zenmanenergy/TeslaTurbine/Pulsejet/200mm/DXF/detonation chamber/spark-plug-61.snapshot.13/Renderings/Spark Plug - side view.png

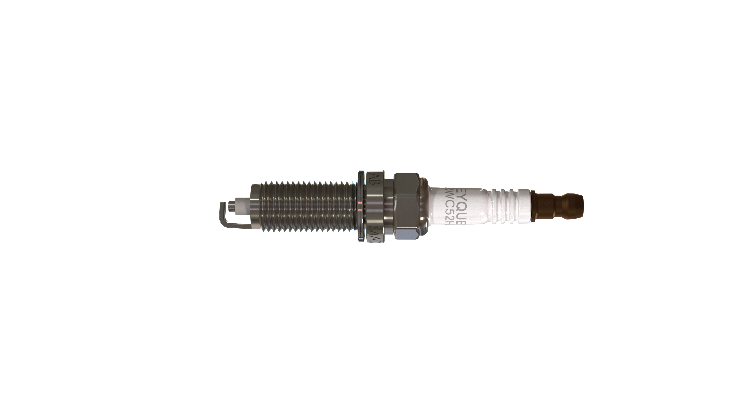
Pulsejet/200mm/DXF/detonation chamber/spark-plug-61.snapshot.13/Renderings/Spark Plug - side view.png
