zenmanenergy/TeslaTurbine/Pulsejet/200mm/DXF/valvular conduit/Tesla-Valve-US1329559-0.png

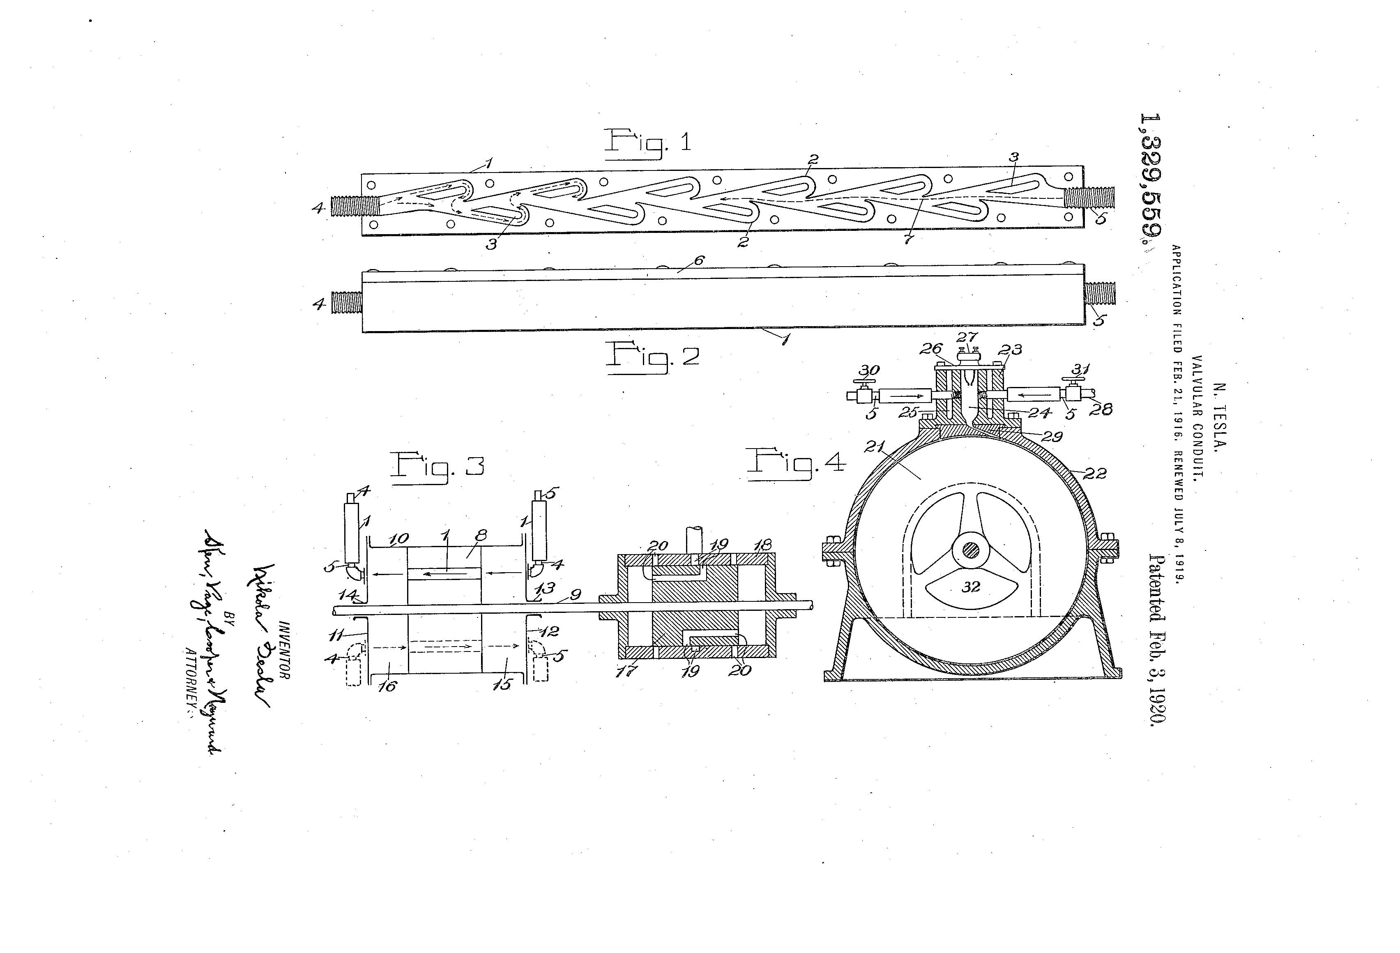
Pulsejet/200mm/DXF/valvular conduit/Tesla-Valve-US1329559-0.png
