zenmanenergy/TeslaTurbine/Pump/138mm/Solidworks 2015/renderings/Tesla Pump.JPG

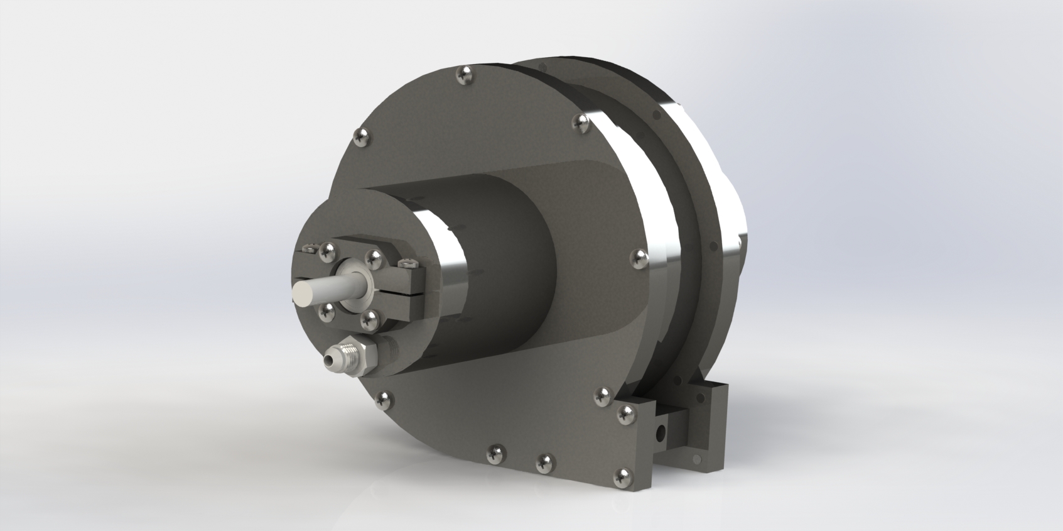
Pump/138mm/Solidworks 2015/renderings/Tesla Pump.JPG
