zenmanenergy/TeslaTurbine/Pulsejet/200mm/DXF/detonation chamber/combustion chamber.SLDASM

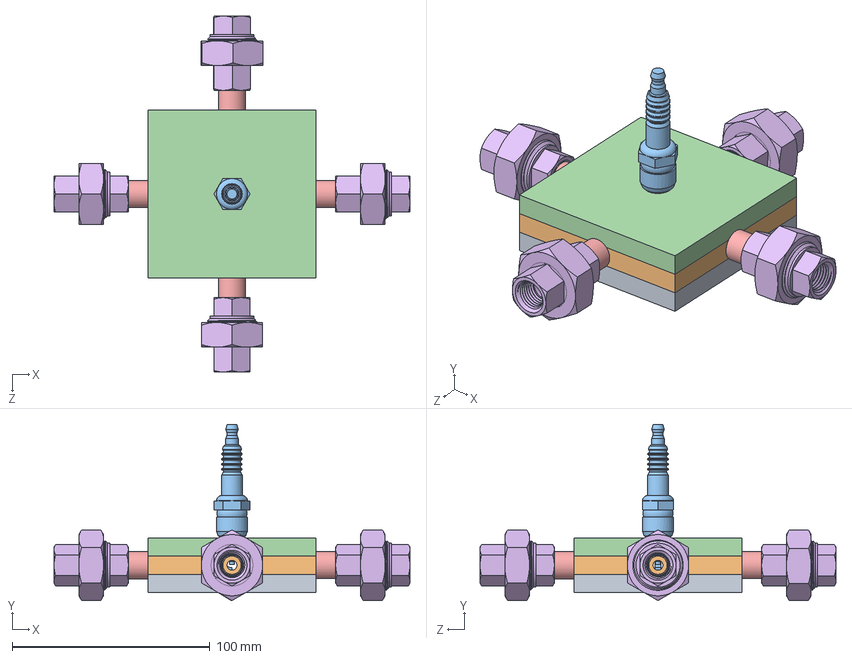
[picture p24: CAD file, 2020-06-17]
Pulsejet/200mm/DXF/detonation chamber/combustion chamber.SLDASM
180.1 x 89.1 x 180.1 mm
combustion chamber
chamber walls
SW3dPS
combustion top
9157K110_STD-WALL 304-304L SS THRD ONE END PIPE NIPPLE x 4
4464K484_TYPE 304 STAINLESS STL THREADED PIPE FITTING x 4
