zenmanenergy/TeslaTurbine/Pump/138mm/Solidworks 2015/magnetic bearings/magnetic bearings.SLDASM

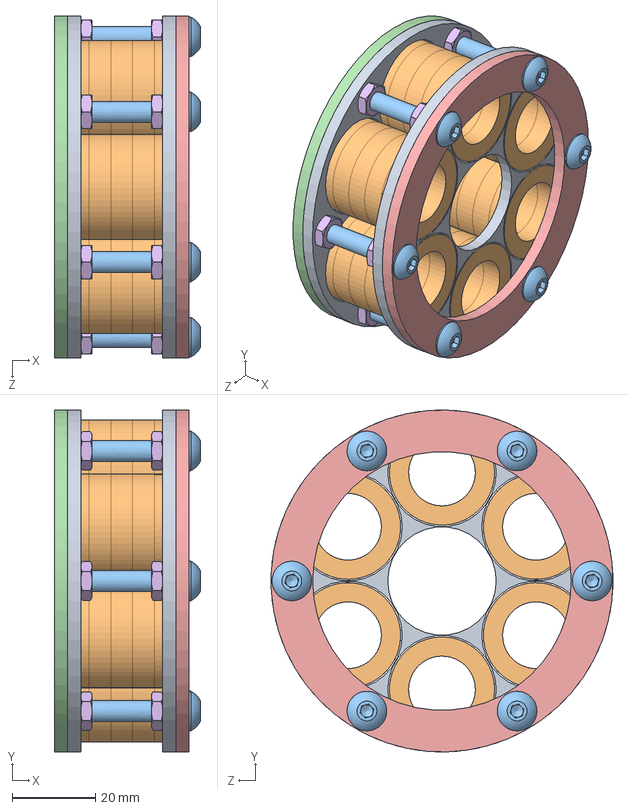
[picture p25: CAD file, 2020-10-07]
Pump/138mm/Solidworks 2015/magnetic bearings/magnetic bearings.SLDASM
35.1 x 82.0 x 82.0 mm
magnet plate x 2
25x16x5 neodymium bearing x 30
socket button head cap screw_am x 6
magnet holder nut
magnet holder
hex nut jam_am x 12
