zenmanenergy/TeslaTurbine/Pulsejet/200mm/DXF/detonation chamber/combustion chamber with propane.SLDASM

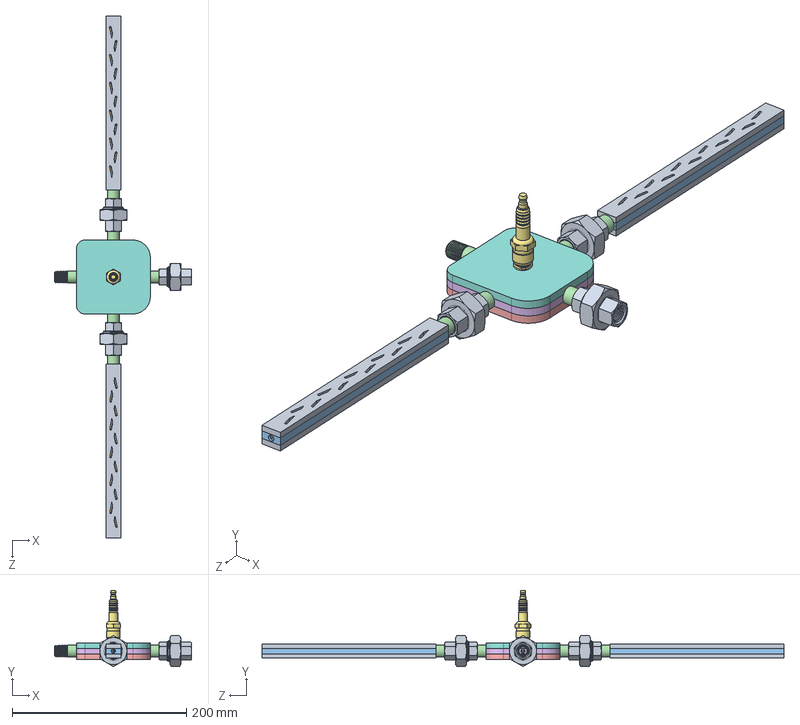
[picture p26: CAD file, 2020-06-17]
Pulsejet/200mm/DXF/detonation chamber/combustion chamber with propane.SLDASM
157.9 x 87.6 x 600.0 mm
bottom x 4
diverter x 22
channel x 2
9157K110_STD-WALL 304-304L SS THRD ONE END PIPE NIPPLE x 6
combustion chamber
chamber walls
SW3dPS
combustion top
4464K484_TYPE 304 STAINLESS STL THREADED PIPE FITTING x 3
