zenmanenergy/TeslaTurbine/Pump/138mm/Solidworks 2015/magnetic bearings/magnetic bearing stack.SLDASM

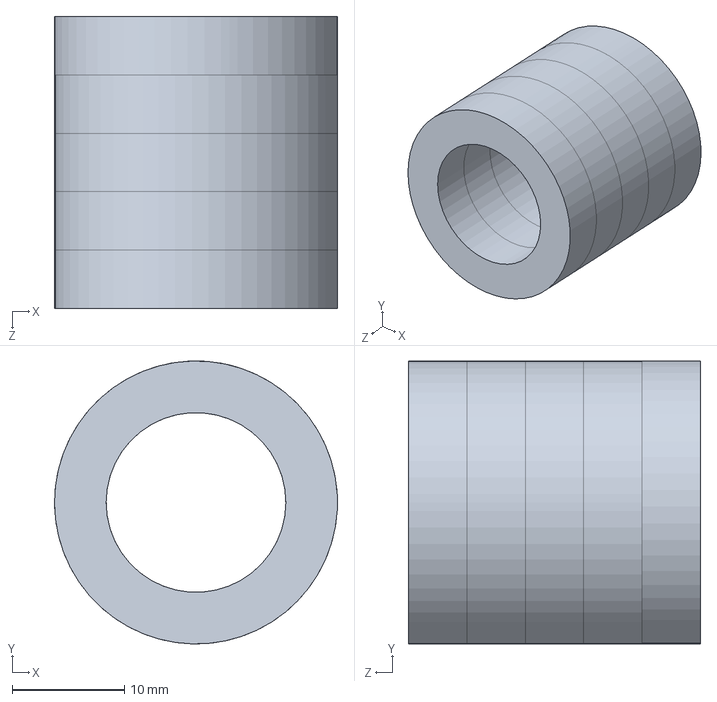
[picture p27: CAD file, 2020-10-07]
Pump/138mm/Solidworks 2015/magnetic bearings/magnetic bearing stack.SLDASM
25.2 x 25.2 x 26.0 mm
25x16x5 neodymium bearing x 5
