zenmanenergy/TeslaTurbine/Pulsejet/200mm/DXF/detonation chamber/combustion top.SLDPRT

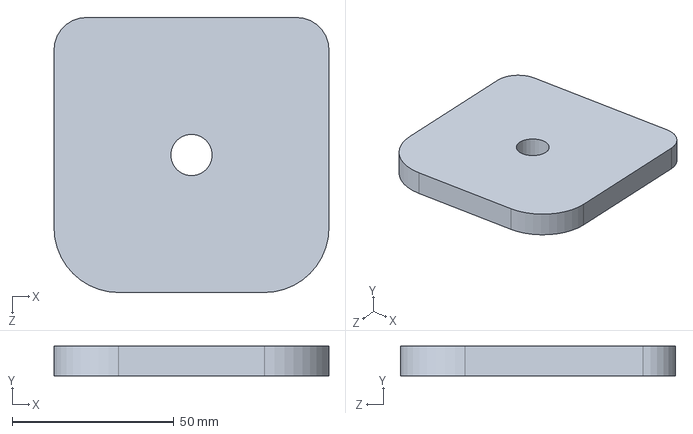
[picture p28: CAD file, 2020-06-17]
Pulsejet/200mm/DXF/detonation chamber/combustion top.SLDPRT
85.0 x 9.20 x 85.0 mm
