zenmanenergy/TeslaTurbine/Pulsejet/200mm/DXF/detonation chamber/Spark Plugs/Spark Plug.STEP

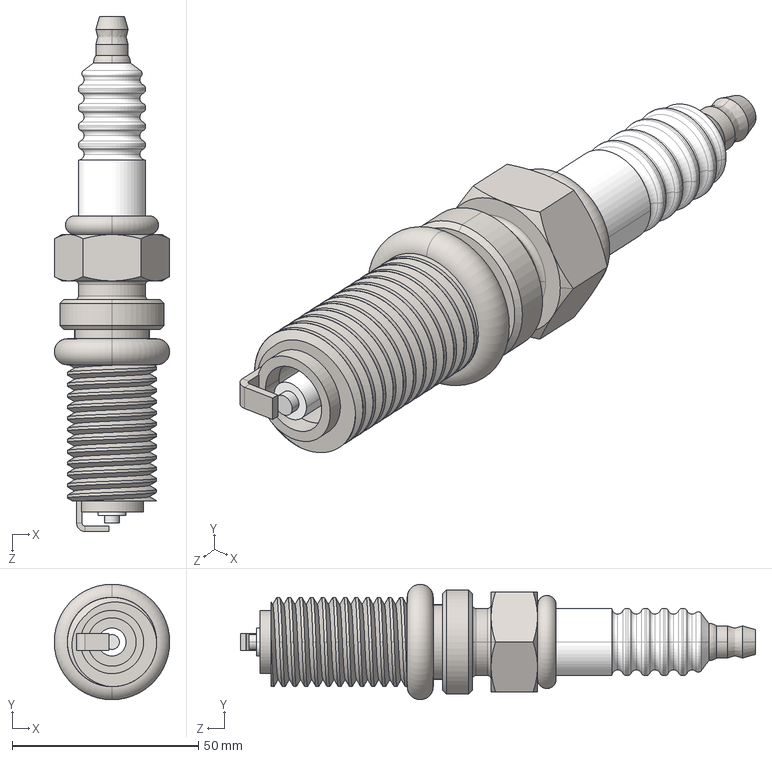
[picture p29: CAD file, 2020-06-17]
Pulsejet/200mm/DXF/detonation chamber/Spark Plugs/Spark Plug.STEP
31.0 x 31.0 x 138.3 mm
