zenmanenergy/TeslaTurbine/Pulsejet/200mm/DXF/detonation chamber/SW3dPS-spark plug/SW3dPS.SLDPRT

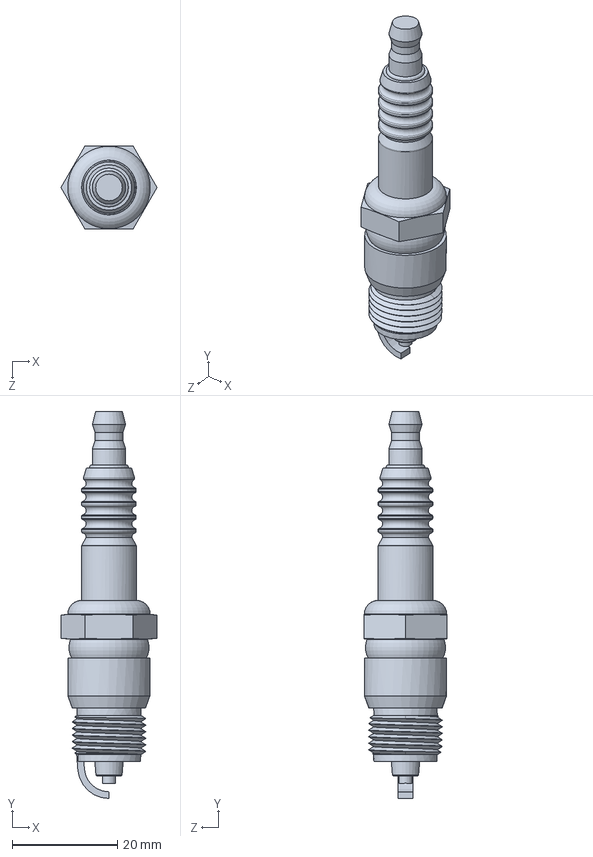
[picture p30: CAD file, 2020-06-17]
Pulsejet/200mm/DXF/detonation chamber/SW3dPS-spark plug/SW3dPS.SLDPRT
18.3 x 73.7 x 15.8 mm
