zenmanenergy/TeslaTurbine/Pulsejet/200mm/DXF/valvular conduit/bottom plate.SLDPRT

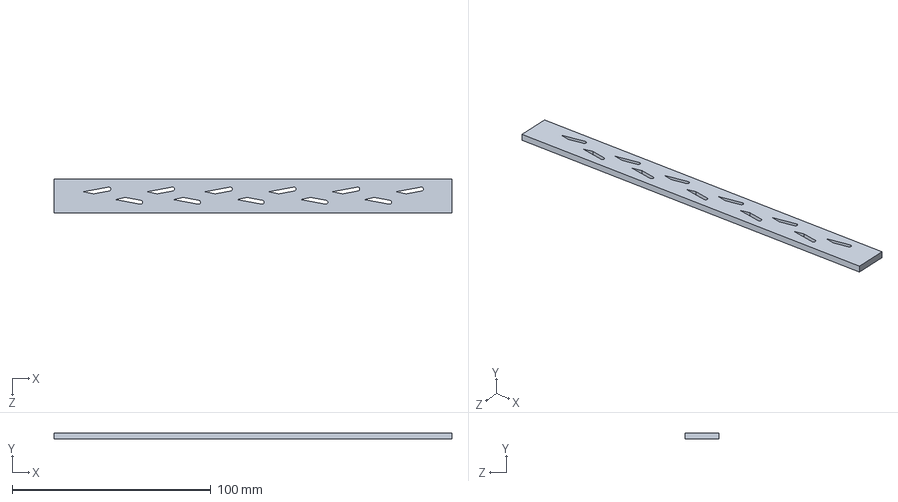
[picture p31: CAD file, 2020-06-17]
Pulsejet/200mm/DXF/valvular conduit/bottom plate.SLDPRT
200.0 x 3.17 x 17.1 mm
