zenmanenergy/TeslaTurbine/Pulsejet/200mm/Solidworks 2015/valvular conduit/bottom.SLDPRT

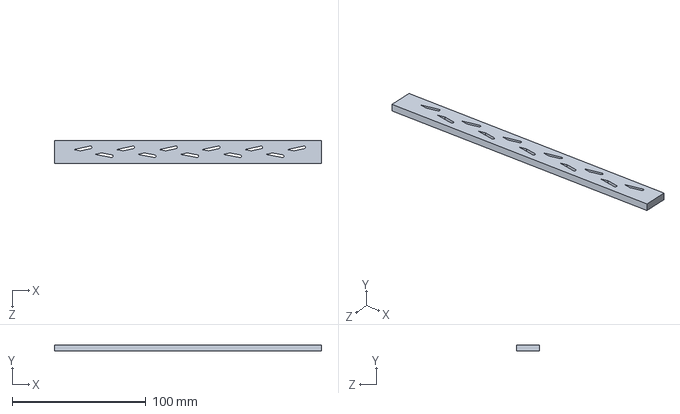
[picture p32: CAD file, 2020-06-17]
Pulsejet/200mm/Solidworks 2015/valvular conduit/bottom.SLDPRT
200.0 x 4.70 x 17.1 mm
