zenmanenergy/TeslaTurbine/Pump/100mm/DXF/bearing mount/bearing mount 1.DXF

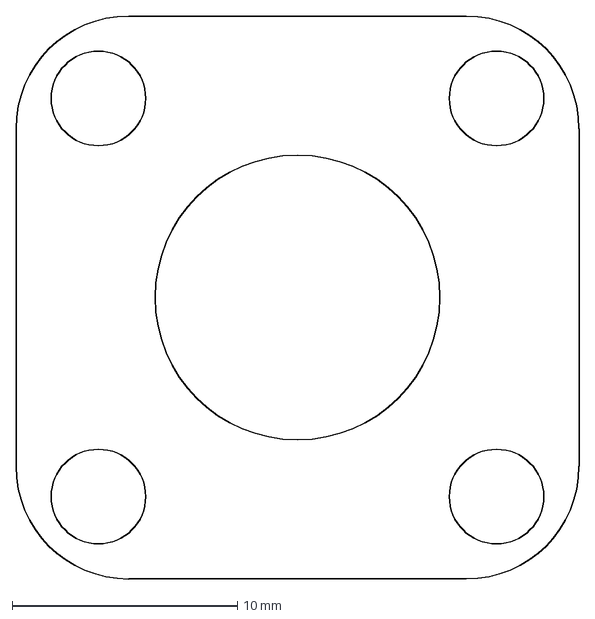
[picture p33: CAD file, 2020-06-16]
Pump/100mm/DXF/bearing mount/bearing mount 1.DXF
25.0 x 25.0 mm
