zenmanenergy/TeslaTurbine/Pump/100mm/DXF/pump stator/housing exhaust 1.DXF

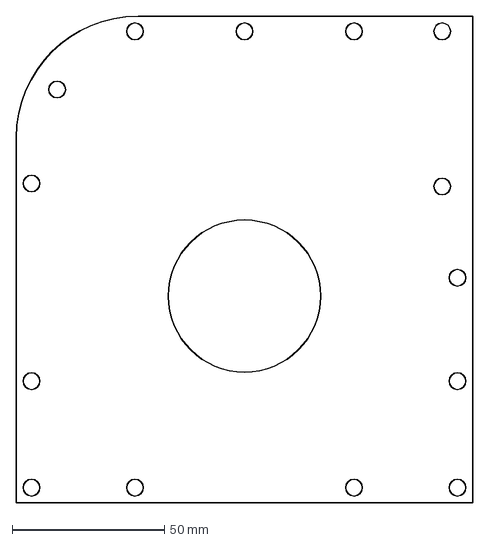
[picture p34: CAD file, 2020-06-16]
Pump/100mm/DXF/pump stator/housing exhaust 1.DXF
150.0 x 160.0 mm
