zenmanenergy/TeslaTurbine/Pump/100mm/DXF/rotor/disk 0.DXF

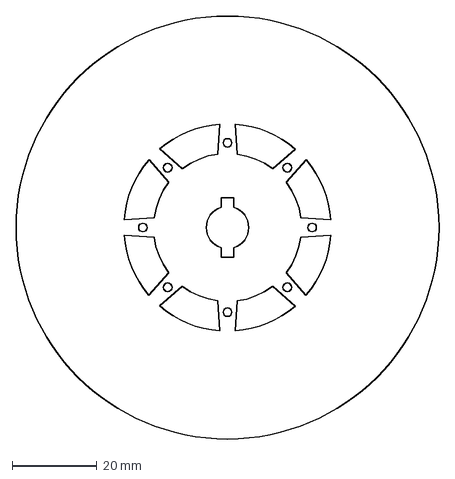
[picture p35: CAD file, 2020-06-16]
Pump/100mm/DXF/rotor/disk 0.DXF
100.0 x 100.0 mm
