zenmanenergy/TeslaTurbine/Pump/100mm/Solidworks 2015/bearing mount/bearing mount 1.SLDPRT

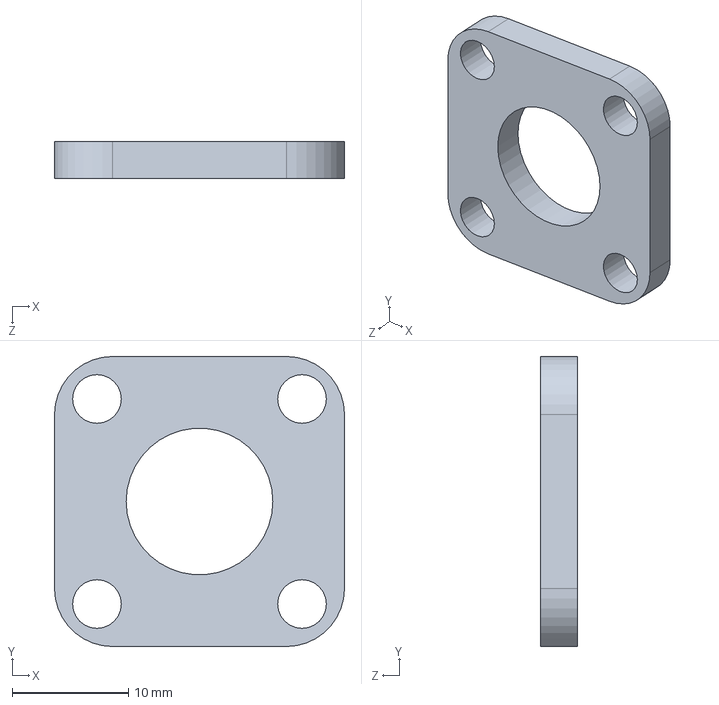
[picture p36: CAD file, 2020-06-16]
Pump/100mm/Solidworks 2015/bearing mount/bearing mount 1.SLDPRT
25.0 x 25.0 x 3.20 mm
