zenmanenergy/TeslaTurbine/Pump/100mm/Solidworks 2015/pump stator/housing exhaust 1.SLDPRT

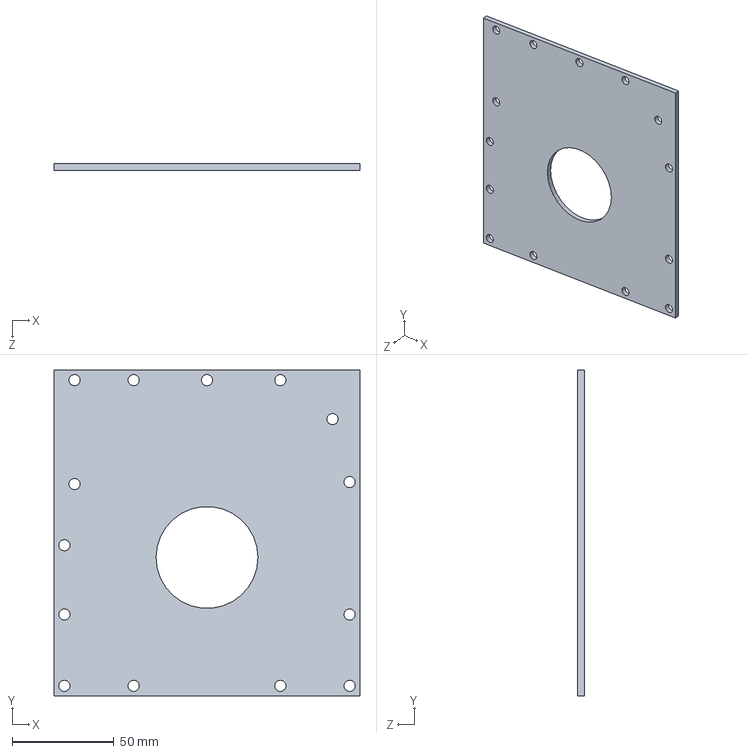
[picture p37: CAD file, 2020-06-29]
Pump/100mm/Solidworks 2015/pump stator/housing exhaust 1.SLDPRT
150.0 x 160.0 x 3.20 mm
