zenmanenergy/TeslaTurbine/Pump/100mm/Solidworks 2015/rotor/axle.SLDPRT

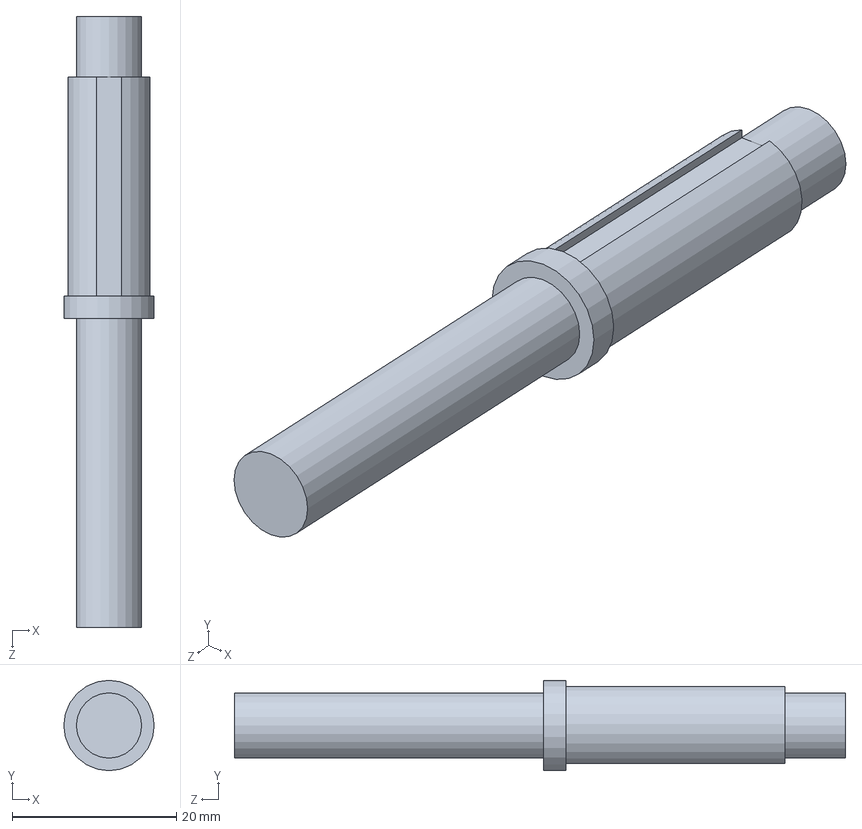
[picture p38: CAD file, 2020-06-29]
Pump/100mm/Solidworks 2015/rotor/axle.SLDPRT
11.0 x 11.0 x 74.3 mm
