zenmanenergy/TeslaTurbine/Pump/138mm/DXF/bearing mount/magnet plate.DXF

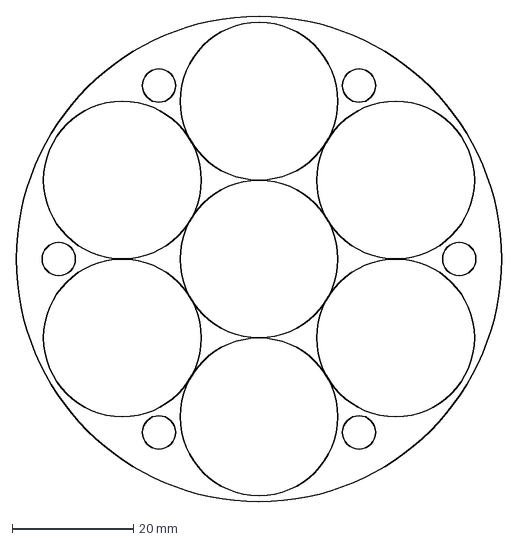
[picture p39: CAD file, 2020-10-07]
Pump/138mm/DXF/bearing mount/magnet plate.DXF
80.0 x 80.0 mm
