zenmanenergy/TeslaTurbine/Pump/138mm/DXF/pump stator/tube end plate.DXF

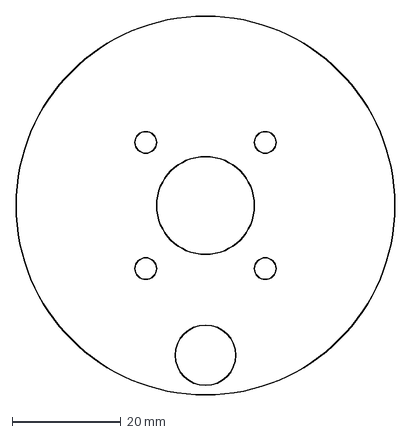
[picture p40: CAD file, 2020-08-22]
Pump/138mm/DXF/pump stator/tube end plate.DXF
69.7 x 69.7 mm
