zenmanenergy/TeslaTurbine/Pump/138mm/DXF/rotor/disk 0.DXF

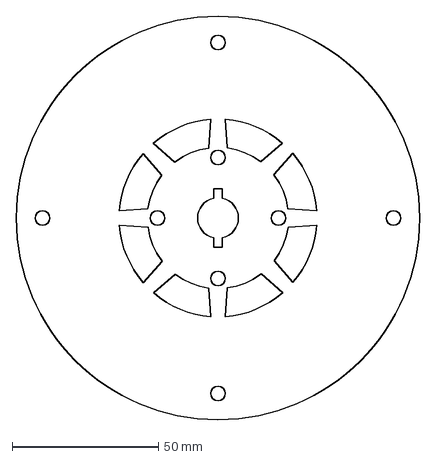
[picture p41: CAD file, 2020-08-04]
Pump/138mm/DXF/rotor/disk 0.DXF
138.0 x 138.0 mm
