zenmanenergy/TeslaTurbine/Pump/138mm/Solidworks 2015/magnetic bearings/magnet plate.SLDPRT

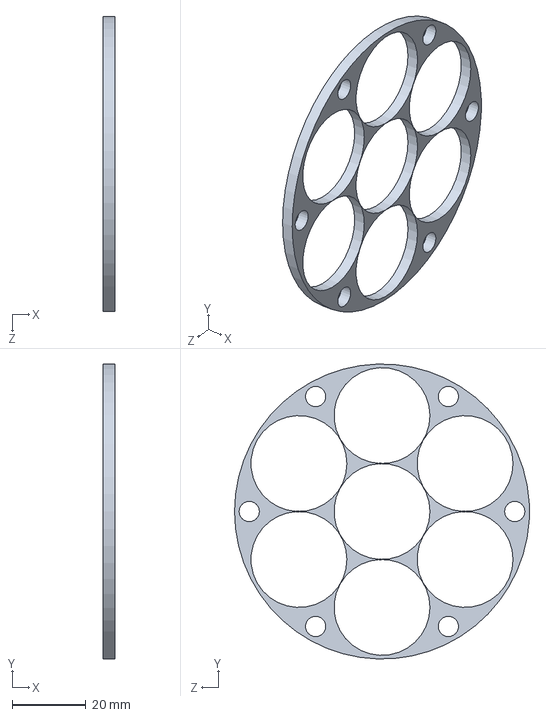
[picture p42: CAD file, 2020-10-07]
Pump/138mm/Solidworks 2015/magnetic bearings/magnet plate.SLDPRT
3.17 x 80.0 x 80.0 mm
