zenmanenergy/TeslaTurbine/Pump/138mm/Solidworks 2015/Motor/Yaegoo DC motor JK-0232 24V 2700RPM.SLDPRT

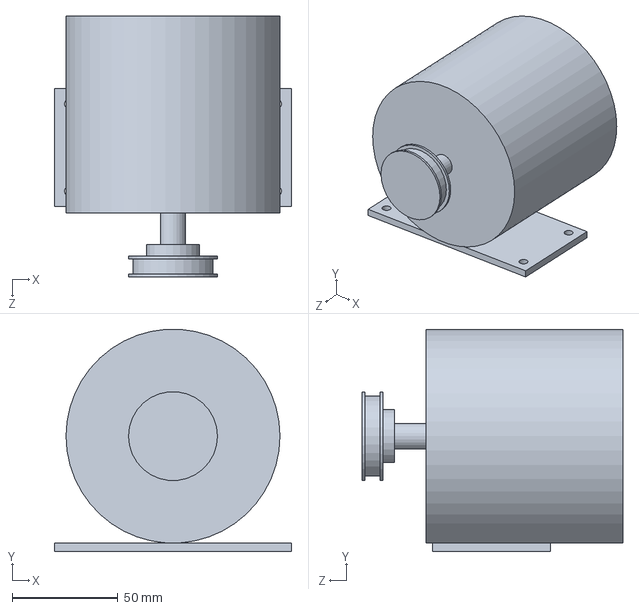
[picture p43: CAD file, 2020-10-07]
Pump/138mm/Solidworks 2015/Motor/Yaegoo DC motor JK-0232 24V 2700RPM.SLDPRT
112.0 x 104.9 x 123.2 mm
