zenmanenergy/TeslaTurbine/Pulsejet/200mm/DXF/detonation chamber/combustion bottom.SLDPRT

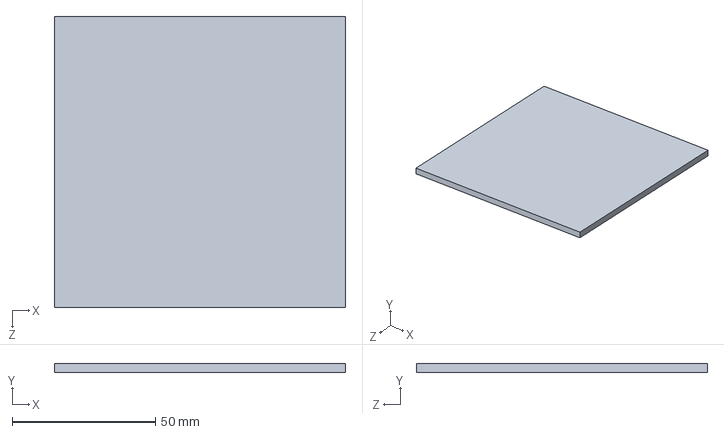
[picture p44: CAD file, 2020-06-17]
Pulsejet/200mm/DXF/detonation chamber/combustion bottom.SLDPRT
101.6 x 3.17 x 101.6 mm
