zenmanenergy/TeslaTurbine/Pulsejet/200mm/DXF/detonation chamber/Spark Plugs/spark plug 1/Insulator.sldprt

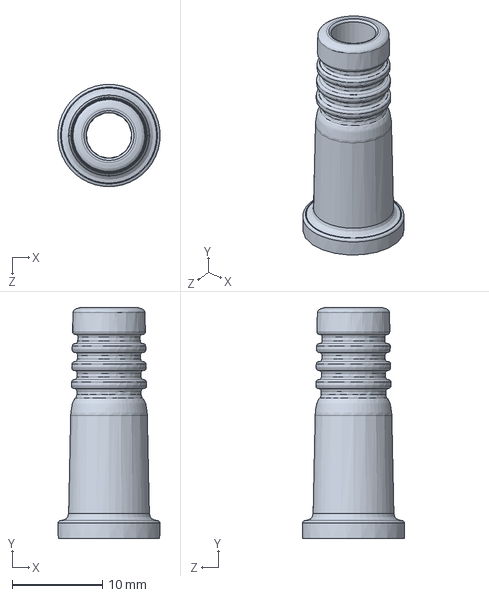
[picture p45: CAD file, 2020-06-17]
Pulsejet/200mm/DXF/detonation chamber/Spark Plugs/spark plug 1/Insulator.sldprt
11.4 x 25.6 x 11.4 mm
