zenmanenergy/TeslaTurbine/Pulsejet/200mm/DXF/valvular conduit/channel.SLDPRT

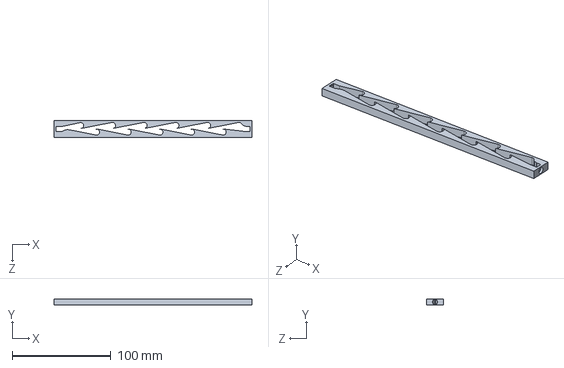
[picture p46: CAD file, 2020-06-17]
Pulsejet/200mm/DXF/valvular conduit/channel.SLDPRT
200.0 x 6.35 x 17.1 mm
