zenmanenergy/TeslaTurbine/Pulsejet/200mm/Solidworks 2015/detonation chamber/detonation middle.SLDPRT

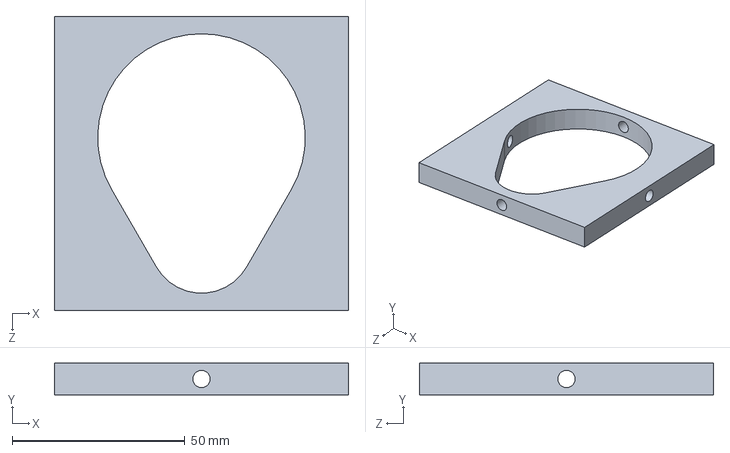
[picture p47: CAD file, 2020-06-17]
Pulsejet/200mm/Solidworks 2015/detonation chamber/detonation middle.SLDPRT
85.0 x 9.20 x 85.0 mm
