zenmanenergy/TeslaTurbine/Pump/100mm/DXF/pump stator/exhaust mount 2.DXF

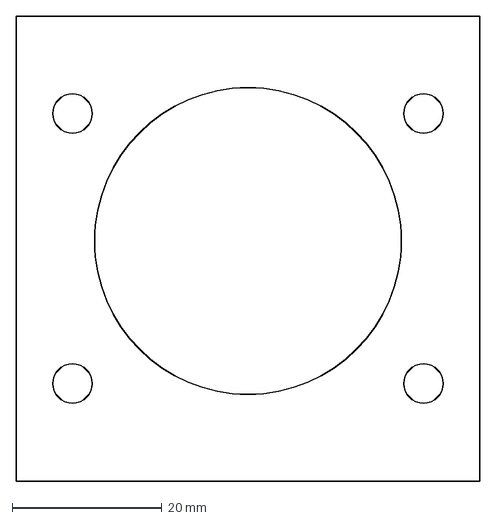
[picture p48: CAD file, 2020-06-16]
Pump/100mm/DXF/pump stator/exhaust mount 2.DXF
61.8 x 62.0 mm
