zenmanenergy/TeslaTurbine/Pump/100mm/DXF/rotor/spacer 1.DXF

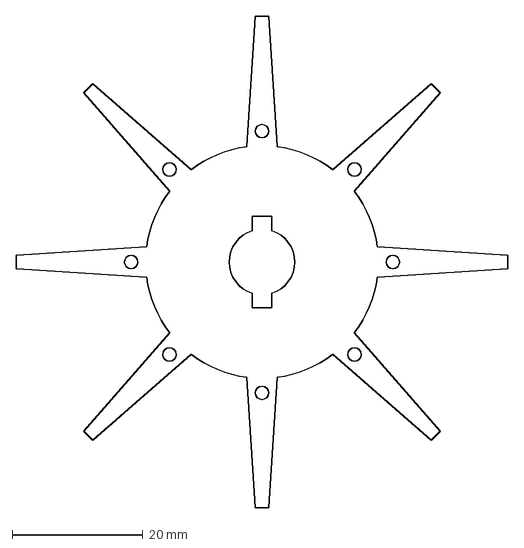
[picture p49: CAD file, 2020-06-16]
Pump/100mm/DXF/rotor/spacer 1.DXF
75.2 x 75.2 mm
