zenmanenergy/TeslaTurbine/Pump/100mm/Solidworks 2015/pump stator/housing1.SLDPRT

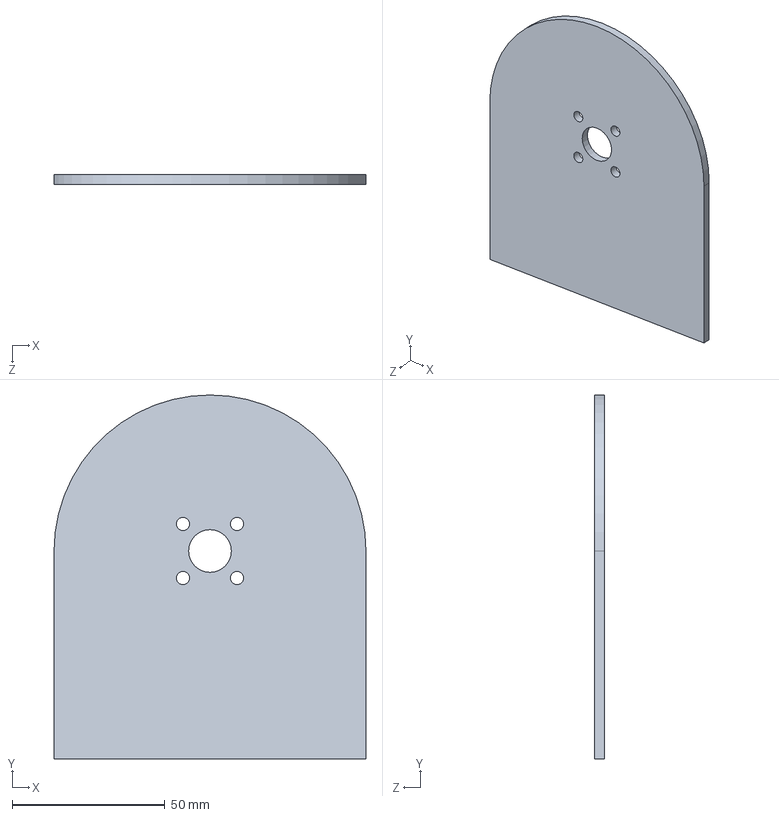
[picture p50: CAD file, 2020-06-29]
Pump/100mm/Solidworks 2015/pump stator/housing1.SLDPRT
102.0 x 119.0 x 3.20 mm
