zenmanenergy/TeslaTurbine/Pump/100mm/Solidworks 2015/Tesla Pump/Lid Input.SLDPRT

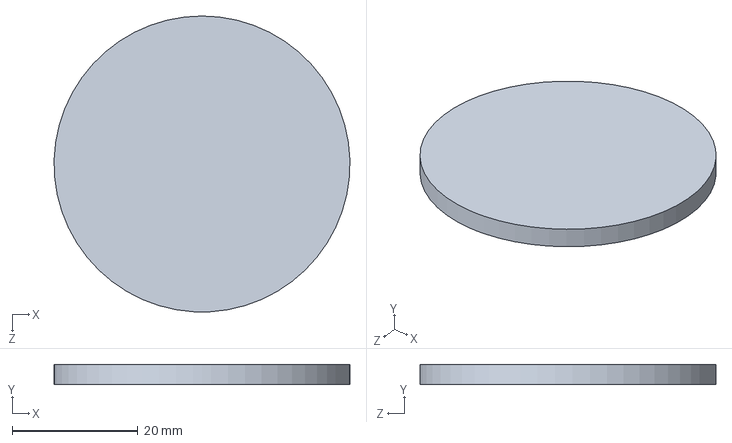
[picture p51: CAD file, 2020-06-16]
Pump/100mm/Solidworks 2015/Tesla Pump/Lid Input.SLDPRT
47.0 x 3.20 x 47.0 mm
