zenmanenergy/TeslaTurbine/Pump/138mm/DXF/bearing mount/bearing compression mount.DXF

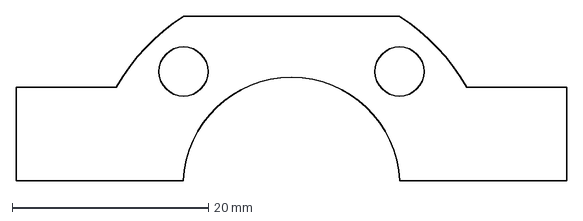
[picture p52: CAD file, 2020-08-04]
Pump/138mm/DXF/bearing mount/bearing compression mount.DXF
56.1 x 16.7 mm
