zenmanenergy/TeslaTurbine/Pump/138mm/DXF/magnetic bearing/magnet holder.DXF

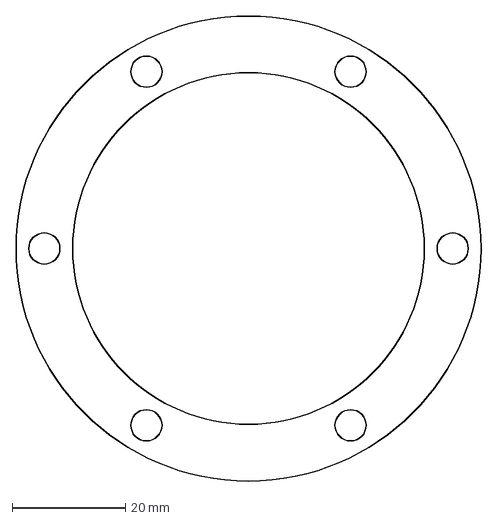
[picture p53: CAD file, 2020-10-07]
Pump/138mm/DXF/magnetic bearing/magnet holder.DXF
82.0 x 82.0 mm
