zenmanenergy/TeslaTurbine/Pump/138mm/DXF/pump stator/Flat pattern - rolled housing.DXF

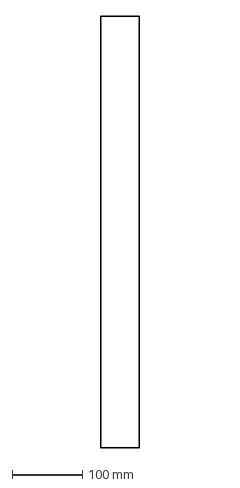
[picture p54: CAD file, 2020-08-22]
Pump/138mm/DXF/pump stator/Flat pattern - rolled housing.DXF
54.0 x 612.1 mm
