zenmanenergy/TeslaTurbine/Pump/138mm/DXF/rotor/disk X input.DXF

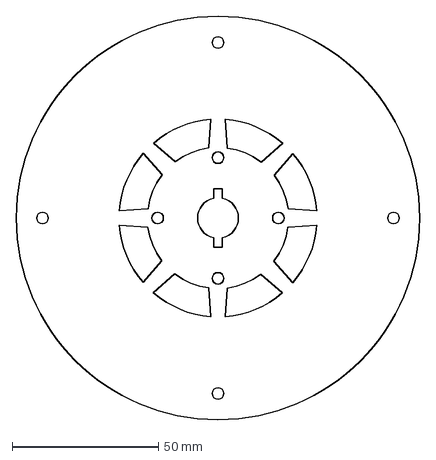
[picture p55: CAD file, 2020-08-04]
Pump/138mm/DXF/rotor/disk X input.DXF
138.0 x 138.0 mm
