zenmanenergy/TeslaTurbine/Pump/138mm/Solidworks 2015/bearing mount/bearing compression mount.SLDPRT

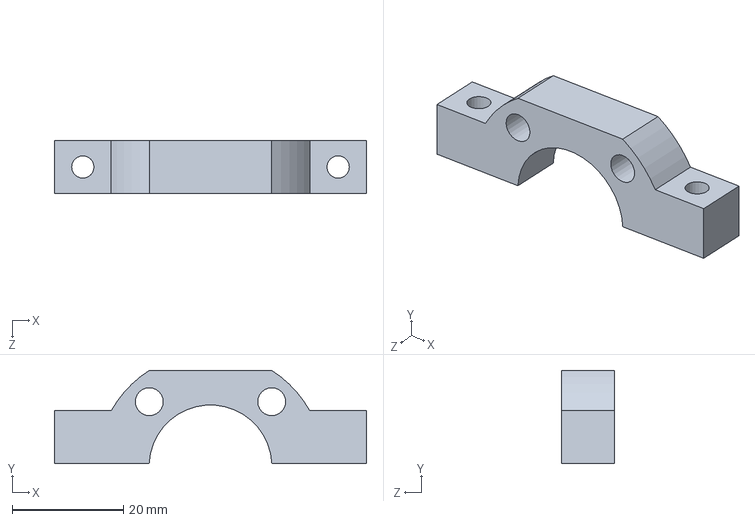
[picture p56: CAD file, 2020-08-22]
Pump/138mm/Solidworks 2015/bearing mount/bearing compression mount.SLDPRT
56.1 x 16.7 x 9.50 mm
