zenmanenergy/TeslaTurbine/Pump/138mm/Solidworks 2015/pump stator/tube end plate.SLDPRT

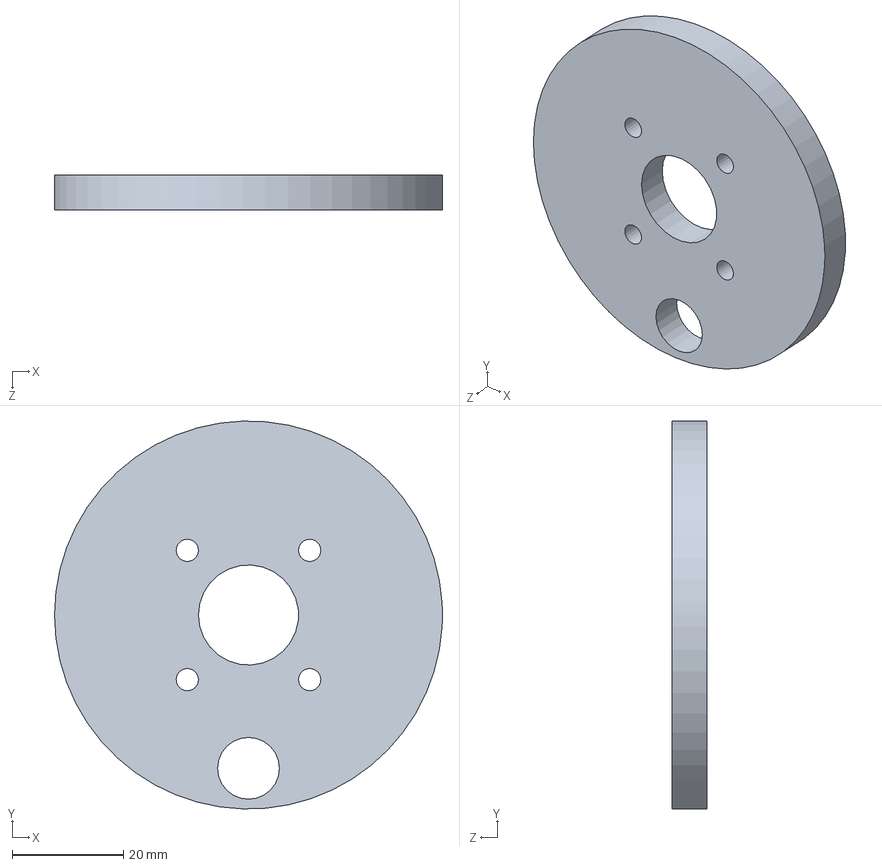
[picture p57: CAD file, 2020-08-22]
Pump/138mm/Solidworks 2015/pump stator/tube end plate.SLDPRT
69.8 x 69.7 x 6.35 mm
