zenmanenergy/TeslaTurbine/Pump/138mm/Solidworks 2015/rotor/disk 0.SLDPRT

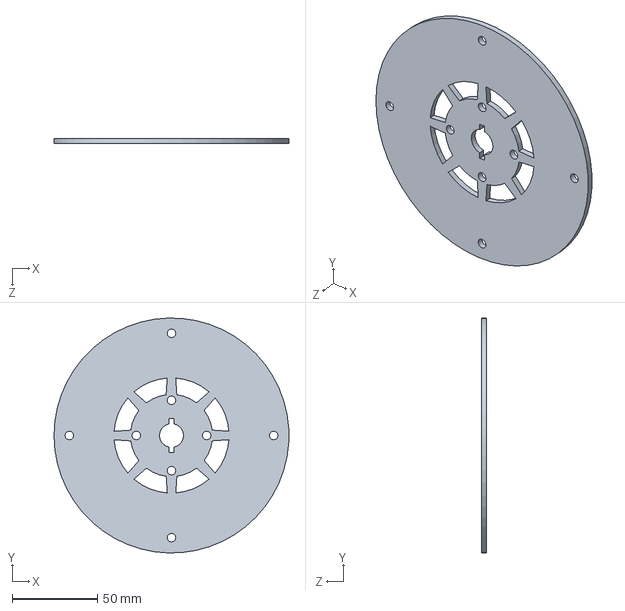
[picture p58: CAD file, 2020-08-22]
Pump/138mm/Solidworks 2015/rotor/disk 0.SLDPRT
138.0 x 137.9 x 3.20 mm
