zenmanenergy/TeslaTurbine/Pulsejet/200mm/DXF/detonation chamber/spark plug.SLDPRT

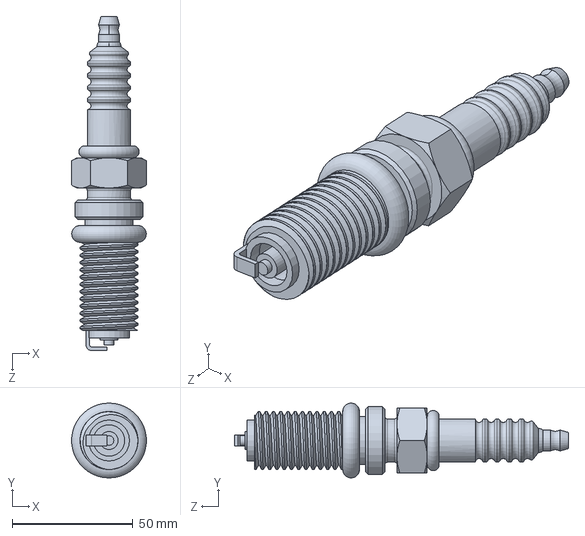
[picture p59: CAD file, 2020-06-17]
Pulsejet/200mm/DXF/detonation chamber/spark plug.SLDPRT
31.0 x 31.0 x 138.2 mm
