zenmanenergy/TeslaTurbine/Pulsejet/200mm/DXF/valvular conduit/diverter.SLDPRT

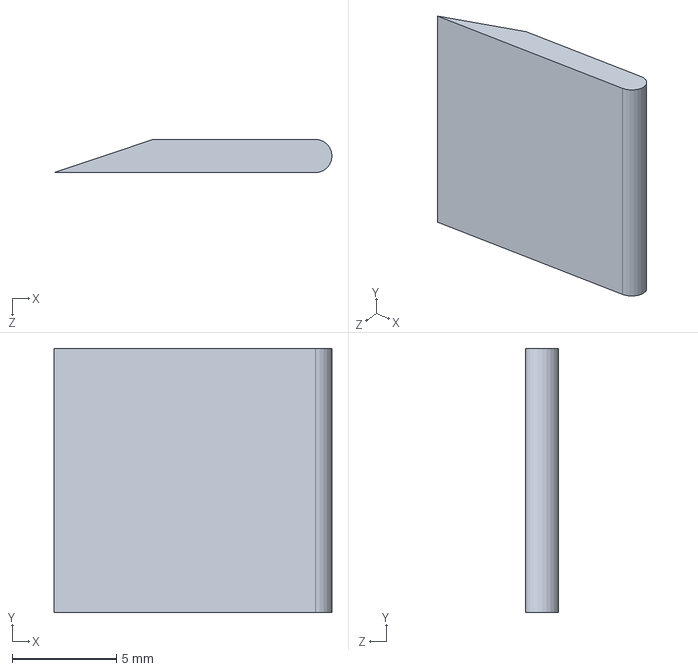
[picture p60: CAD file, 2020-06-17]
Pulsejet/200mm/DXF/valvular conduit/diverter.SLDPRT
13.4 x 12.7 x 1.60 mm
