zenmanenergy/TeslaTurbine/Pump/100mm/DXF/pump stator/input mount 2.DXF

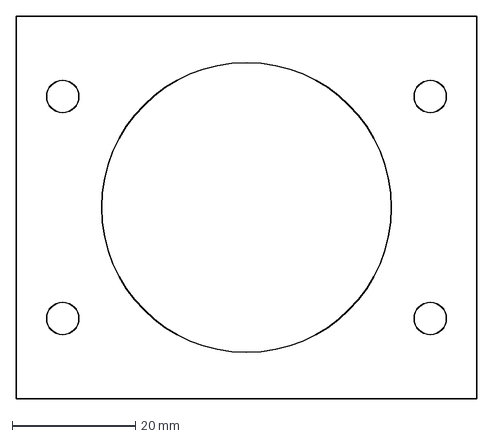
[picture p61: CAD file, 2020-06-16]
Pump/100mm/DXF/pump stator/input mount 2.DXF
74.6 x 62.0 mm
