zenmanenergy/TeslaTurbine/Pump/100mm/DXF/rotor/disk 1.DXF

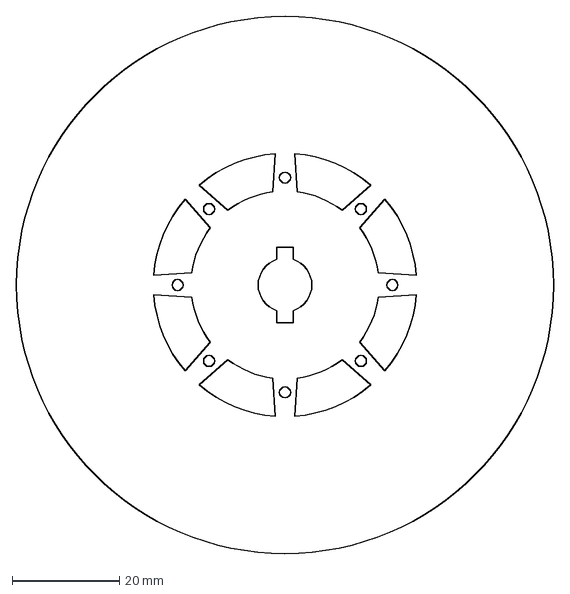
[picture p62: CAD file, 2020-06-16]
Pump/100mm/DXF/rotor/disk 1.DXF
100.0 x 100.0 mm
