zenmanenergy/TeslaTurbine/Pump/100mm/Solidworks 2015/pump stator/housing 5.SLDPRT

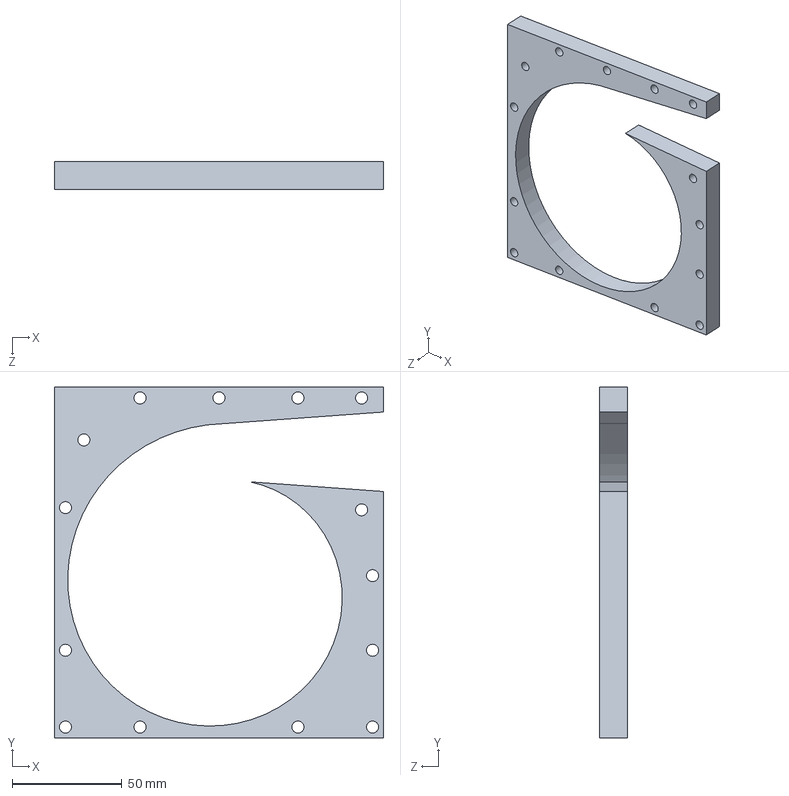
[picture p63: CAD file, 2020-06-29]
Pump/100mm/Solidworks 2015/pump stator/housing 5.SLDPRT
150.0 x 160.0 x 12.7 mm
