zenmanenergy/TeslaTurbine/Pump/100mm/Solidworks 2015/rotor/disk 0.SLDPRT

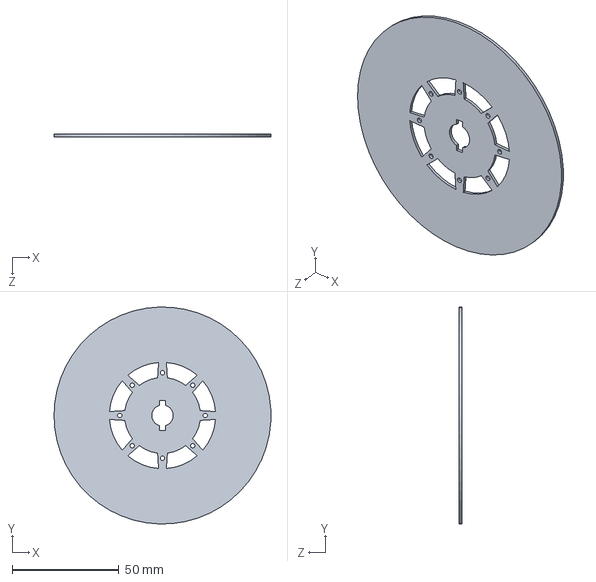
[picture p64: CAD file, 2020-06-16]
Pump/100mm/Solidworks 2015/rotor/disk 0.SLDPRT
101.6 x 101.6 x 1.22 mm
