zenmanenergy/TeslaTurbine/Pump/138mm/DXF/magnetic bearing/magnet plate.DXF

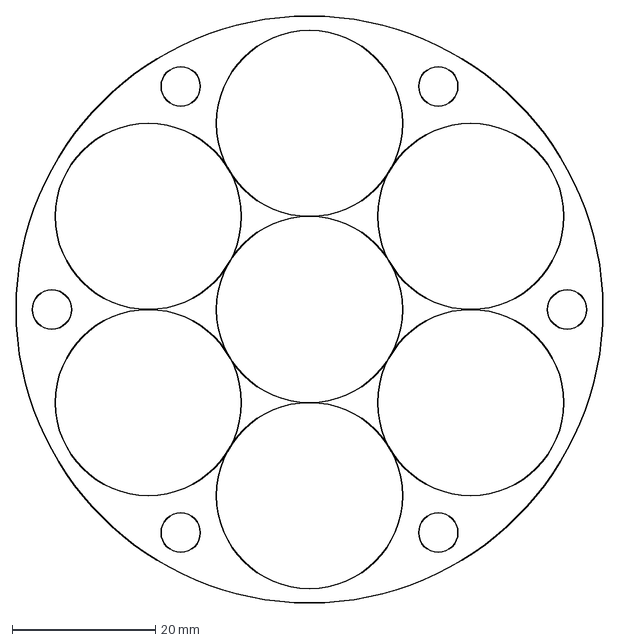
[picture p65: CAD file, 2020-10-07]
Pump/138mm/DXF/magnetic bearing/magnet plate.DXF
82.0 x 82.0 mm
