zenmanenergy/TeslaTurbine/Pump/138mm/DXF/pump stator/mounting ring.DXF

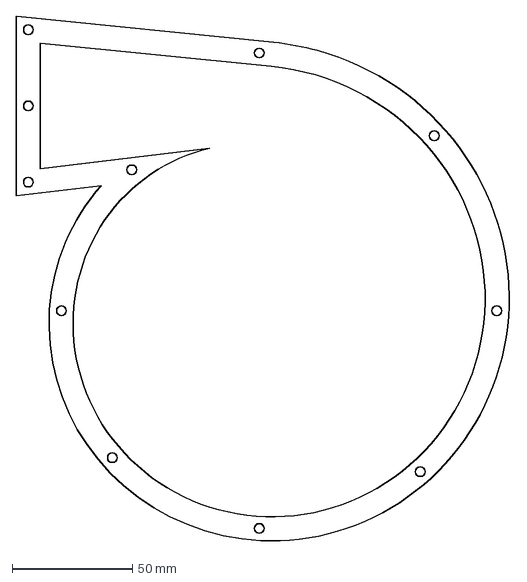
[picture p66: CAD file, 2020-08-22]
Pump/138mm/DXF/pump stator/mounting ring.DXF
205.4 x 218.2 mm
