zenmanenergy/TeslaTurbine/Pump/138mm/DXF/rotor/disk x.DXF

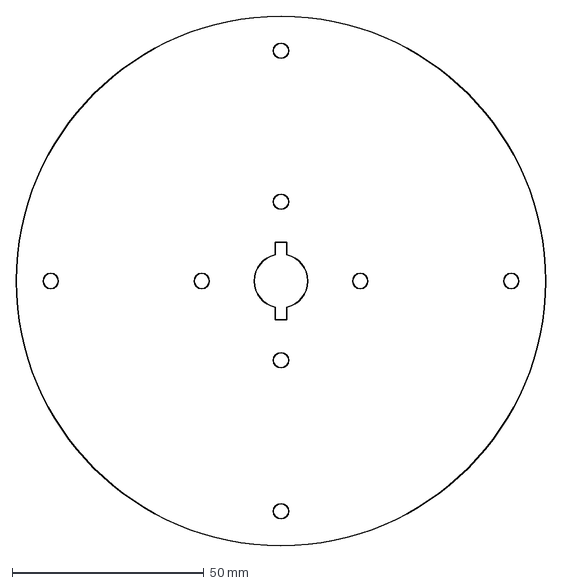
[picture p67: CAD file, 2020-08-04]
Pump/138mm/DXF/rotor/disk x.DXF
138.0 x 138.0 mm
