zenmanenergy/TeslaTurbine/Pump/138mm/Solidworks 2015/bearing mount/pan cross head_am_10.sldprt

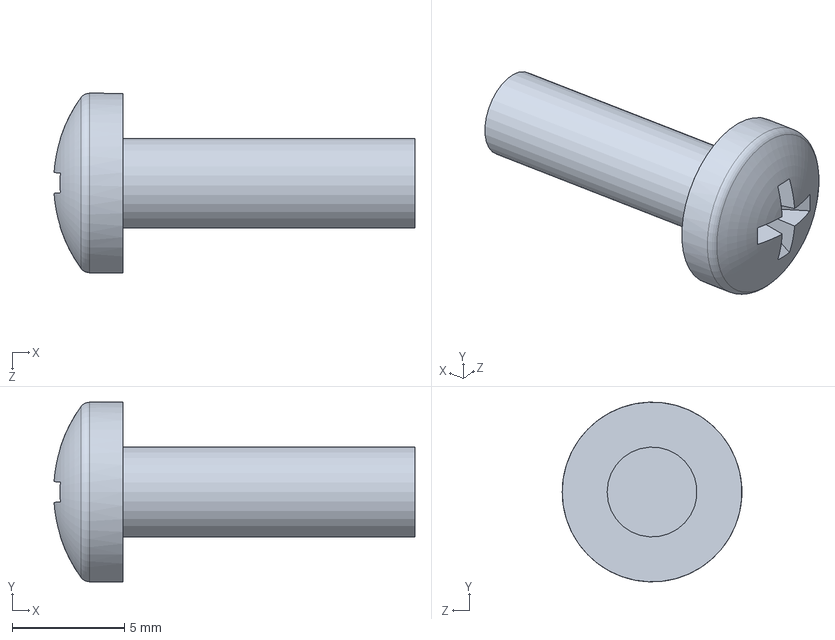
[picture p68: CAD file, 2020-08-04]
Pump/138mm/Solidworks 2015/bearing mount/pan cross head_am_10.sldprt
16.1 x 8.00 x 7.99 mm
