zenmanenergy/TeslaTurbine/Pump/138mm/Solidworks 2015/magnetic bearings/bearing stack holder.SLDPRT

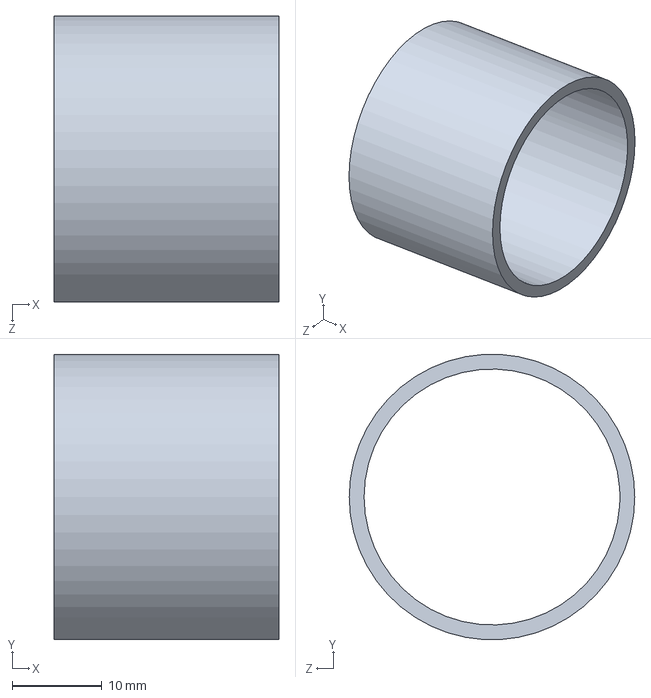
[picture p69: CAD file, 2020-10-07]
Pump/138mm/Solidworks 2015/magnetic bearings/bearing stack holder.SLDPRT
25.0 x 31.7 x 31.8 mm
