zenmanenergy/TeslaTurbine/Pump/138mm/Solidworks 2015/pump stator/rolled housing.SLDPRT

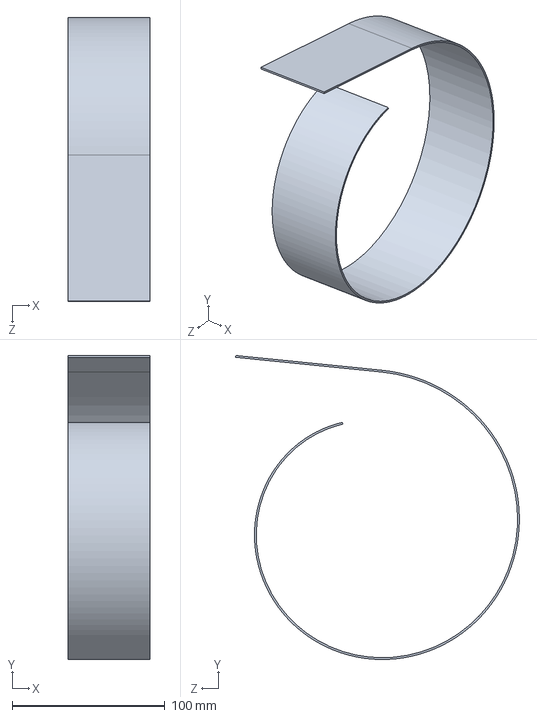
[picture p70: CAD file, 2020-08-22]
Pump/138mm/Solidworks 2015/pump stator/rolled housing.SLDPRT
54.0 x 199.2 x 186.0 mm
