zenmanenergy/TeslaTurbine/Pump/100mm/DXF/pump stator/housing input.DXF

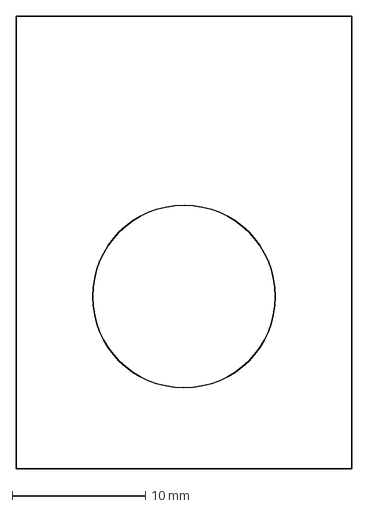
[picture p72: CAD file, 2020-06-16]
Pump/100mm/DXF/pump stator/housing input.DXF
25.2 x 34.0 mm
