zenmanenergy/TeslaTurbine/Pump/100mm/DXF/rotor/keyway.SLDPRT

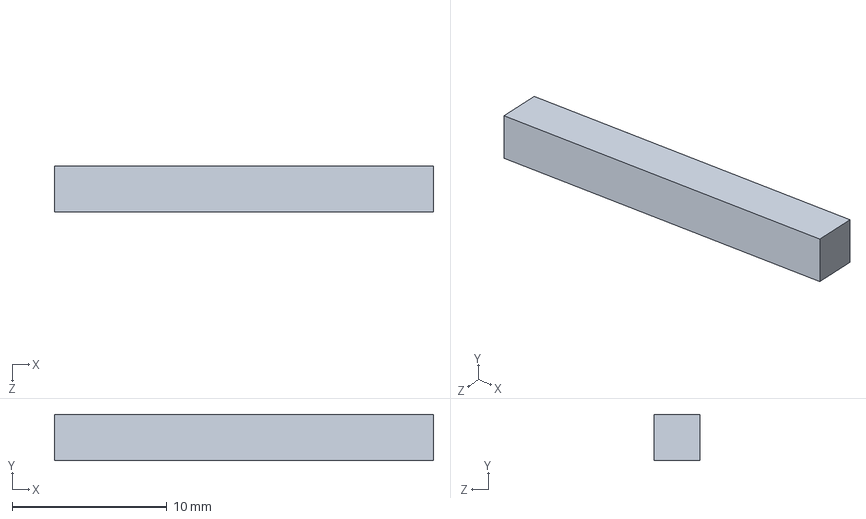
[picture p73: CAD file, 2020-06-16]
Pump/100mm/DXF/rotor/keyway.SLDPRT
24.5 x 3.00 x 3.00 mm
