zenmanenergy/TeslaTurbine/Pump/100mm/Solidworks 2015/rotor/disk 1.SLDPRT

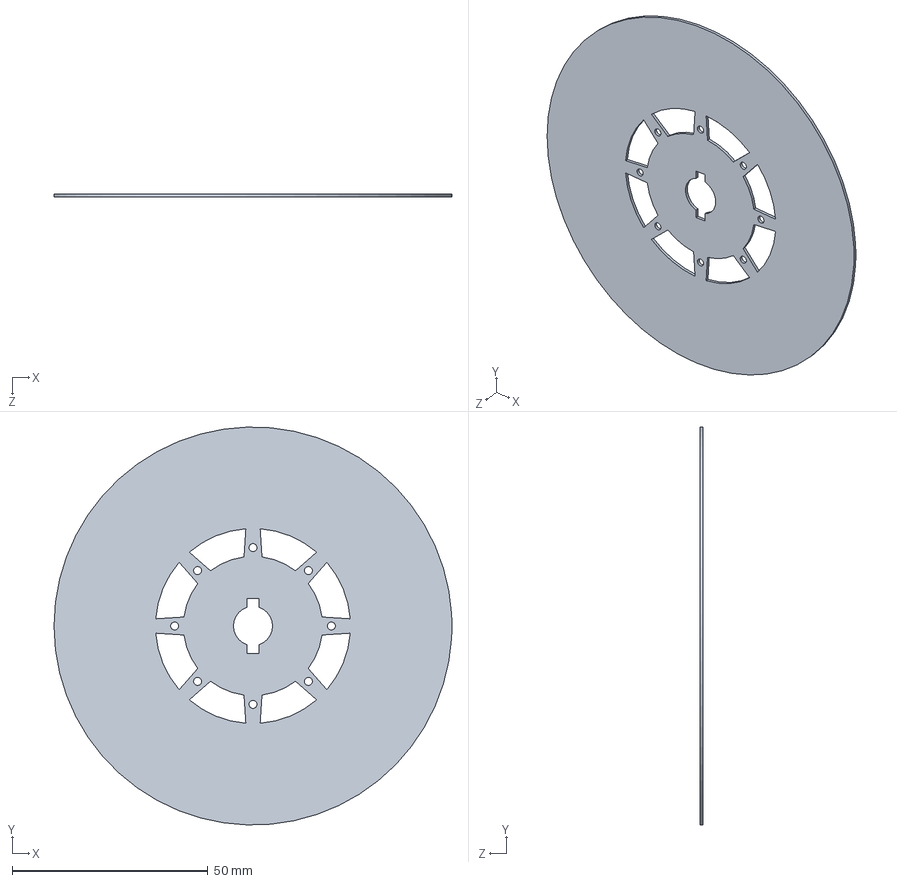
[picture p74: CAD file, 2020-06-16]
Pump/100mm/Solidworks 2015/rotor/disk 1.SLDPRT
101.6 x 101.6 x 0.8 mm
