zenmanenergy/TeslaTurbine/Pump/138mm/DXF/pump stator/exhaust plate.DXF

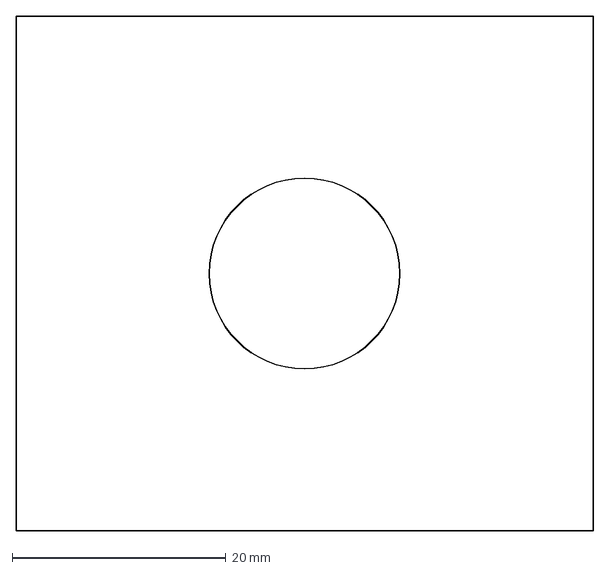
[picture p75: CAD file, 2020-08-22]
Pump/138mm/DXF/pump stator/exhaust plate.DXF
54.0 x 48.1 mm
