zenmanenergy/TeslaTurbine/Pump/138mm/DXF/rotor/disk 1.DXF

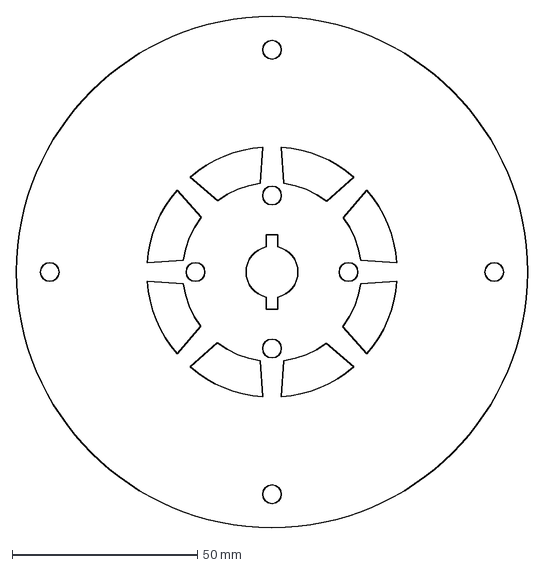
[picture p76: CAD file, 2020-08-04]
Pump/138mm/DXF/rotor/disk 1.DXF
138.0 x 138.0 mm
