zenmanenergy/TeslaTurbine/Pump/138mm/Solidworks 2015/magnetic bearings/magnet holder.SLDPRT

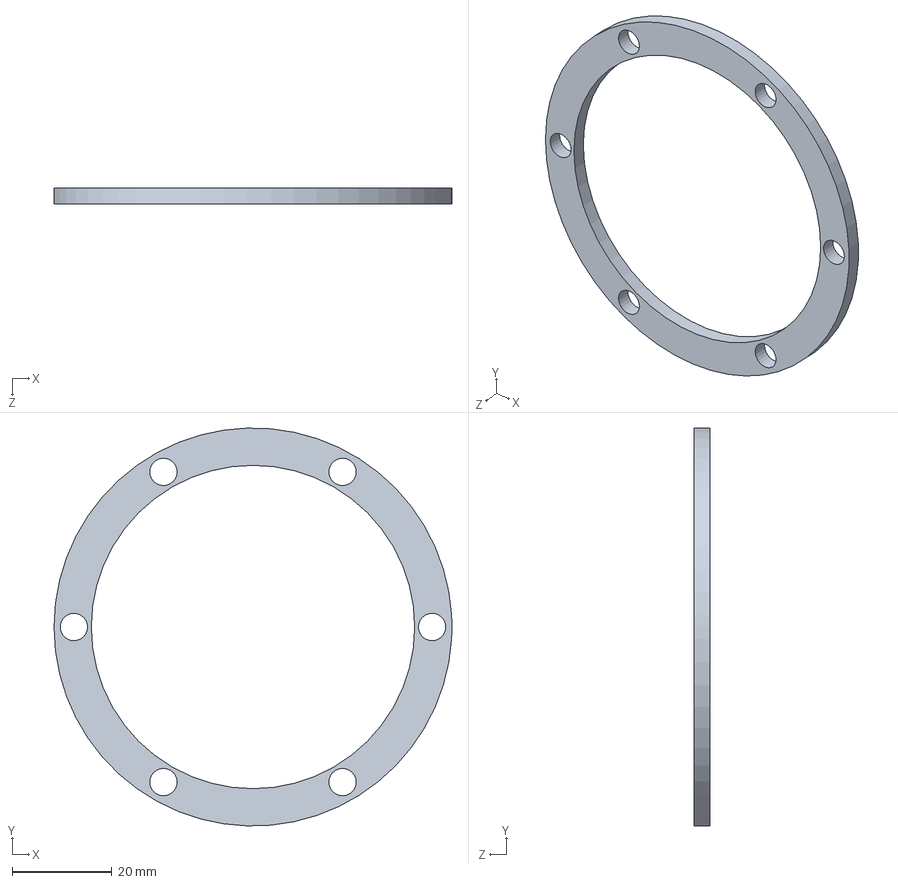
[picture p77: CAD file, 2020-10-07]
Pump/138mm/Solidworks 2015/magnetic bearings/magnet holder.SLDPRT
80.0 x 80.0 x 3.17 mm
