zenmanenergy/TeslaTurbine/Pump/138mm/Solidworks 2015/rotor/keyway.SLDPRT

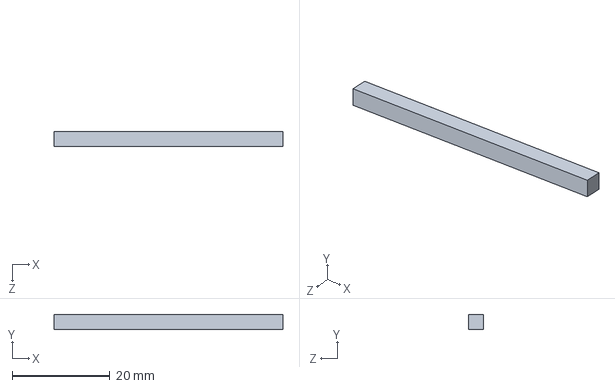
[picture p79: CAD file, 2020-08-04]
Pump/138mm/Solidworks 2015/rotor/keyway.SLDPRT
46.9 x 3.00 x 3.00 mm
