zenmanenergy/TeslaTurbine/Pump/100mm/DXF/pump stator/housing 5.DXF

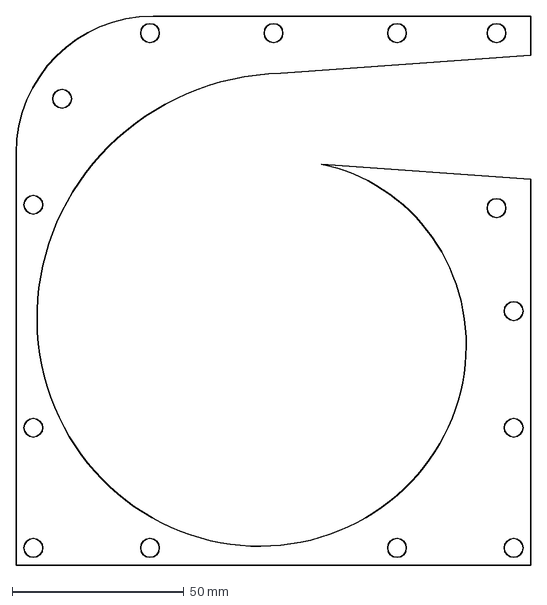
[picture p80: CAD file, 2020-06-16]
Pump/100mm/DXF/pump stator/housing 5.DXF
150.0 x 160.0 mm
