zenmanenergy/TeslaTurbine/Pump/100mm/DXF/rotor/axle.SLDPRT

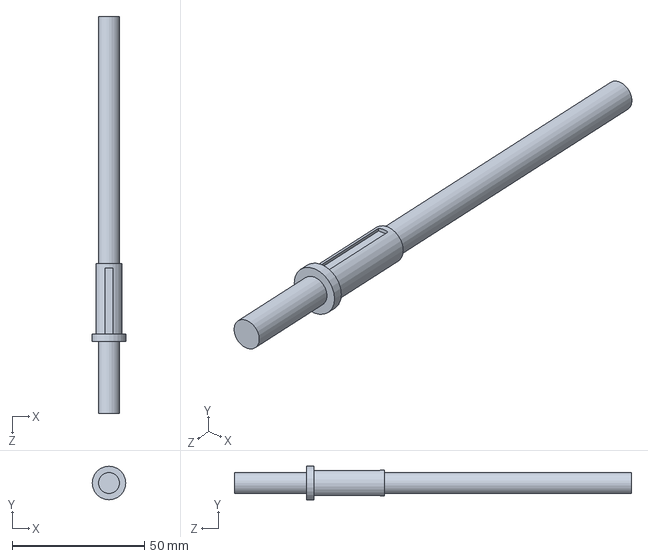
[picture p81: CAD file, 2020-06-16]
Pump/100mm/DXF/rotor/axle.SLDPRT
12.7 x 12.7 x 150.0 mm
