zenmanenergy/TeslaTurbine/Pump/100mm/Solidworks 2015/pump stator/input mount 1.SLDPRT

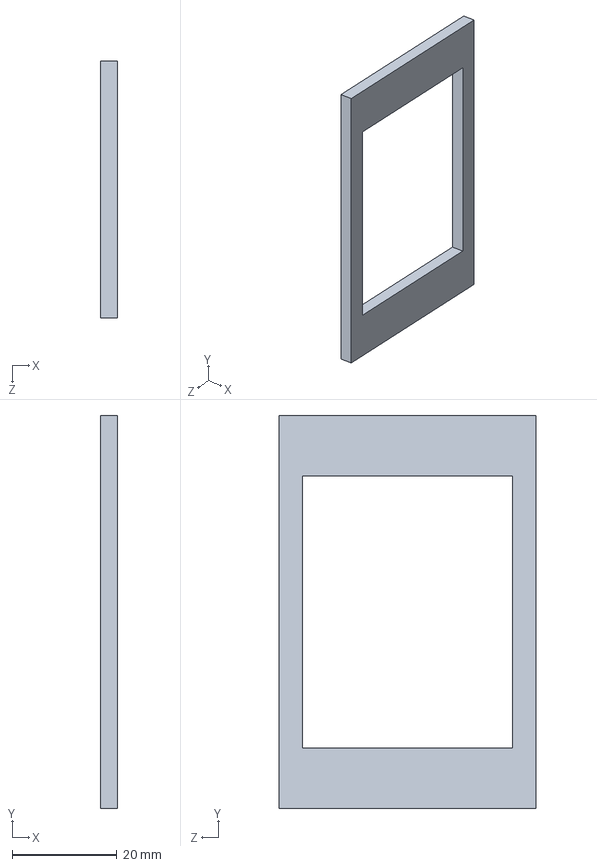
[picture p82: CAD file, 2020-06-29]
Pump/100mm/Solidworks 2015/pump stator/input mount 1.SLDPRT
3.20 x 75.0 x 49.0 mm
