zenmanenergy/TeslaTurbine/Pump/138mm/DXF/pump stator/exhaust plate top.DXF

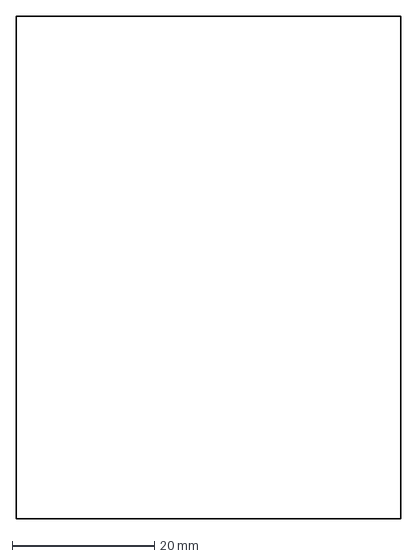
[picture p83: CAD file, 2020-08-22]
Pump/138mm/DXF/pump stator/exhaust plate top.DXF
54.0 x 70.7 mm
