zenmanenergy/TeslaTurbine/Pump/138mm/DXF/rotor/spacer 1.DXF

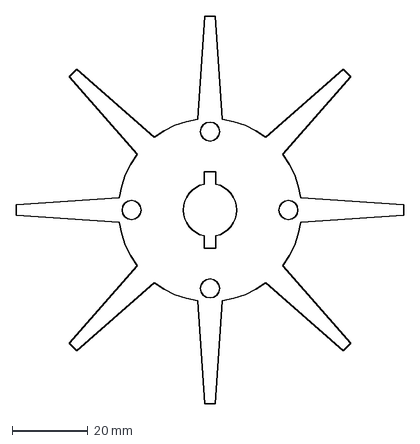
[picture p84: CAD file, 2020-08-04]
Pump/138mm/DXF/rotor/spacer 1.DXF
102.1 x 102.1 mm
