zenmanenergy/TeslaTurbine/Pump/138mm/Solidworks 2015/hardware/pan cross head_am_m4x8.sldprt

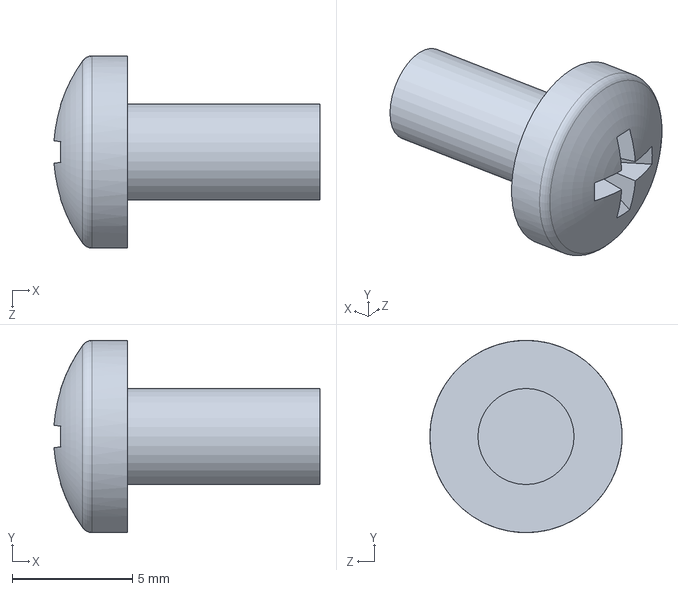
[picture p85: CAD file, 2020-08-04]
Pump/138mm/Solidworks 2015/hardware/pan cross head_am_m4x8.sldprt
11.1 x 8.00 x 8.00 mm
