zenmanenergy/TeslaTurbine/Pump/138mm/Solidworks 2015/pump stator/exhaust plate.SLDPRT

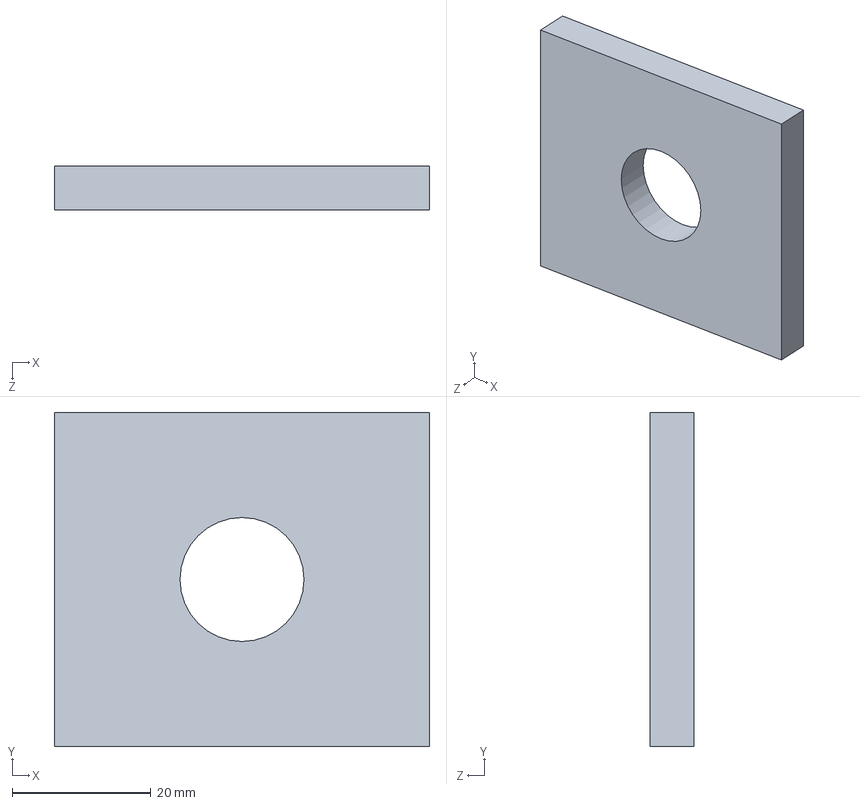
[picture p86: CAD file, 2020-08-22]
Pump/138mm/Solidworks 2015/pump stator/exhaust plate.SLDPRT
54.0 x 48.1 x 6.30 mm
