zenmanenergy/TeslaTurbine/Pump/138mm/Solidworks 2015/rotor/disk 1.SLDPRT

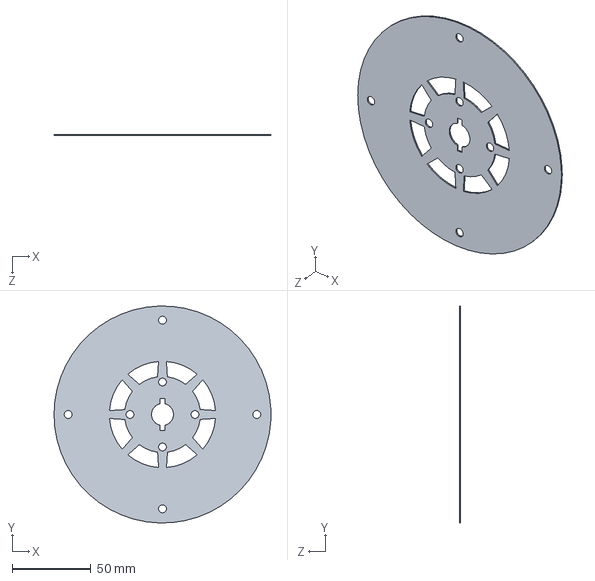
[picture p87: CAD file, 2020-08-04]
Pump/138mm/Solidworks 2015/rotor/disk 1.SLDPRT
138.0 x 137.9 x 0.8 mm
