zenmanenergy/TeslaTurbine/Pump/100mm/Solidworks 2015/pump stator/input mount 2.SLDPRT

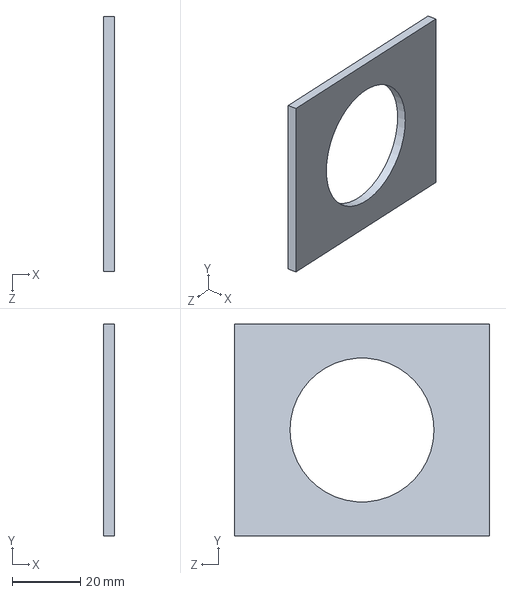
[picture p88: CAD file, 2020-06-29]
Pump/100mm/Solidworks 2015/pump stator/input mount 2.SLDPRT
3.20 x 62.0 x 74.6 mm
