zenmanenergy/TeslaTurbine/Pump/100mm/Solidworks 2015/rotor/spacer 1.SLDPRT

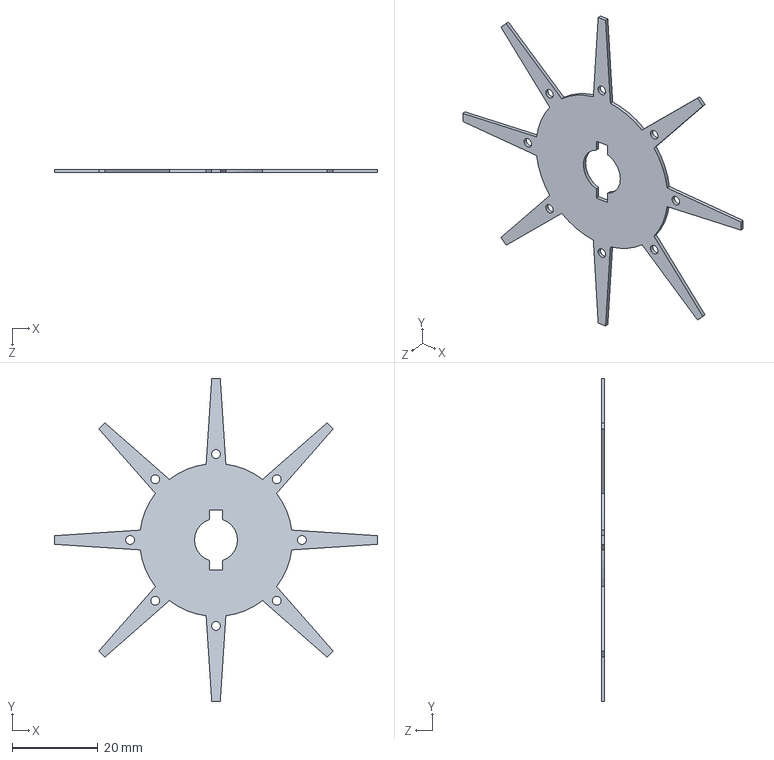
[picture p89: CAD file, 2020-06-16]
Pump/100mm/Solidworks 2015/rotor/spacer 1.SLDPRT
75.2 x 75.2 x 0.8 mm
