zenmanenergy/TeslaTurbine/Pump/138mm/DXF/pump stator/end plate.DXF

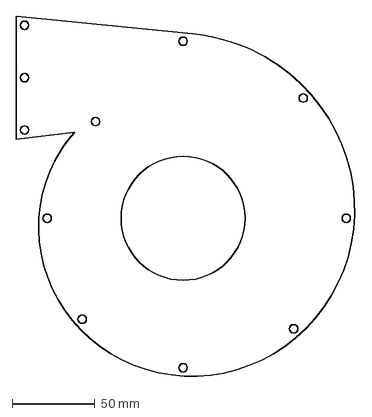
[picture p90: CAD file, 2020-08-22]
Pump/138mm/DXF/pump stator/end plate.DXF
205.4 x 218.2 mm
