zenmanenergy/TeslaTurbine/Pump/138mm/Solidworks 2015/pump stator/exhaust plate top.SLDPRT

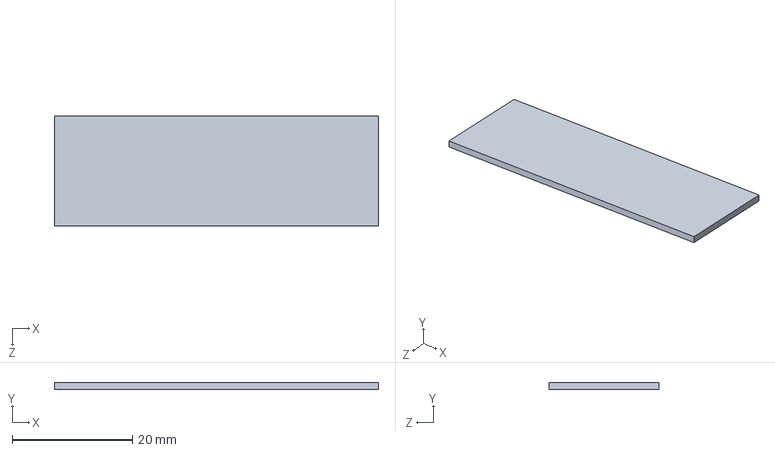
[picture p91: CAD file, 2020-08-22]
Pump/138mm/Solidworks 2015/pump stator/exhaust plate top.SLDPRT
54.0 x 1.20 x 18.4 mm
