zenmanenergy/TeslaTurbine/Pump/138mm/Solidworks 2015/rotor/spacer 1.SLDPRT

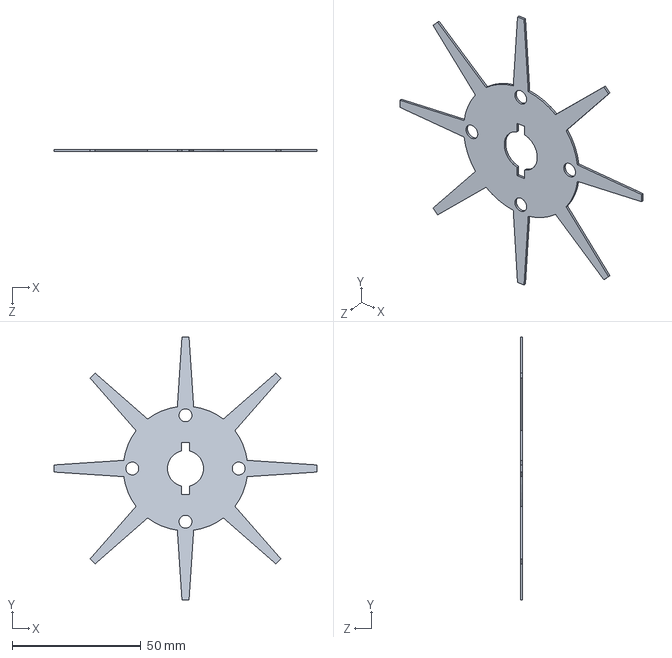
[picture p92: CAD file, 2020-08-04]
Pump/138mm/Solidworks 2015/rotor/spacer 1.SLDPRT
102.1 x 102.1 x 0.8 mm
