zenmanenergy/TeslaTurbine/Pump/100mm/DXF/pump stator/exhaust mount.DXF

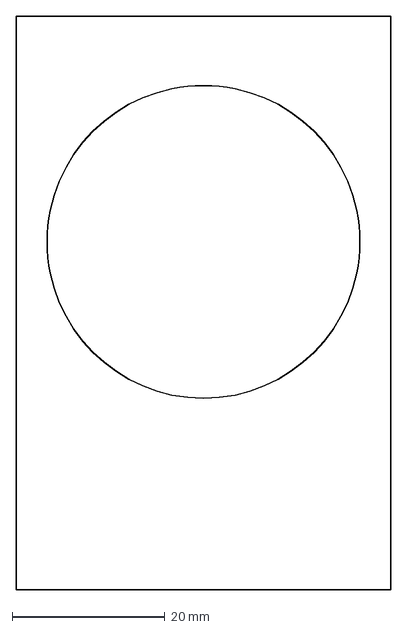
[picture p93: CAD file, 2020-06-16]
Pump/100mm/DXF/pump stator/exhaust mount.DXF
49.0 x 75.0 mm
