zenmanenergy/TeslaTurbine/Pump/138mm/DXF/pump stator/Flat pattern - bearing pipe.DXF

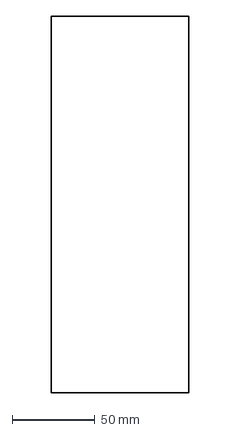
[picture p95: CAD file, 2020-08-04]
Pump/138mm/DXF/pump stator/Flat pattern - bearing pipe.DXF
83.0 x 226.9 mm
