zenmanenergy/TeslaTurbine/Pump/138mm/Solidworks 2015/magnetic bearings/bearing ring.SLDPRT

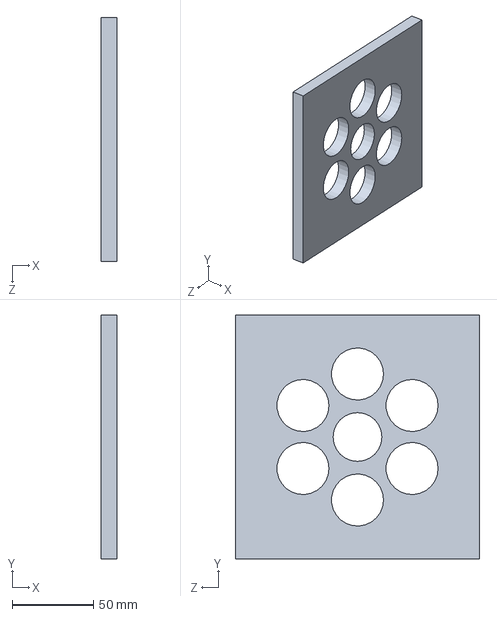
[picture p96: CAD file, 2020-10-07]
Pump/138mm/Solidworks 2015/magnetic bearings/bearing ring.SLDPRT
10.0 x 150.0 x 150.0 mm
