zenmanenergy/TeslaTurbine/Pump/138mm/Solidworks 2015/pump stator/end plate.SLDPRT

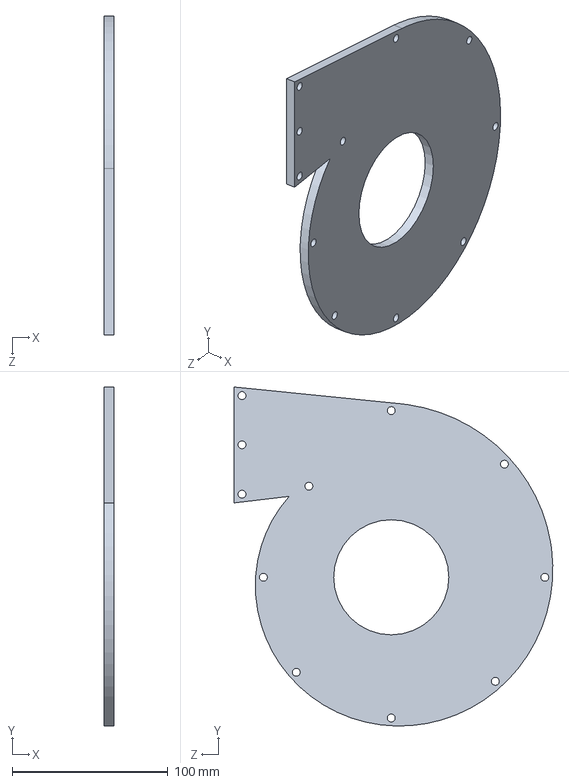
[picture p97: CAD file, 2020-08-22]
Pump/138mm/Solidworks 2015/pump stator/end plate.SLDPRT
6.35 x 217.9 x 204.7 mm
