zenmanenergy/TeslaTurbine/Pump/138mm/Solidworks 2015/rotor/axle.SLDPRT

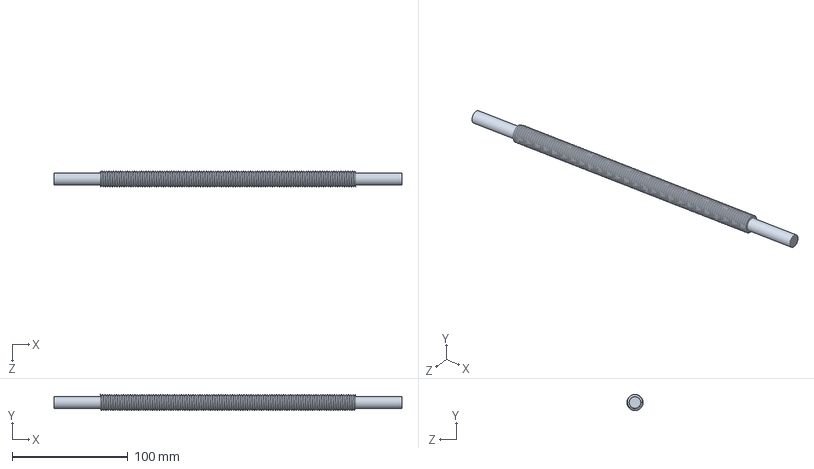
[picture p98: CAD file, 2020-08-04]
Pump/138mm/Solidworks 2015/rotor/axle.SLDPRT
300.0 x 14.0 x 14.0 mm
