zenmanenergy/TeslaTurbine/Pump/100mm/DXF/pump stator/exhaust mount 1.DXF

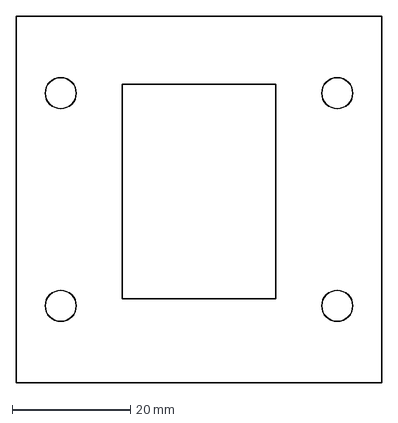
[picture p99: CAD file, 2020-06-16]
Pump/100mm/DXF/pump stator/exhaust mount 1.DXF
61.8 x 62.0 mm
