zenmanenergy/TeslaTurbine/Pump/138mm/DXF/pump stator/end plate 1.DXF

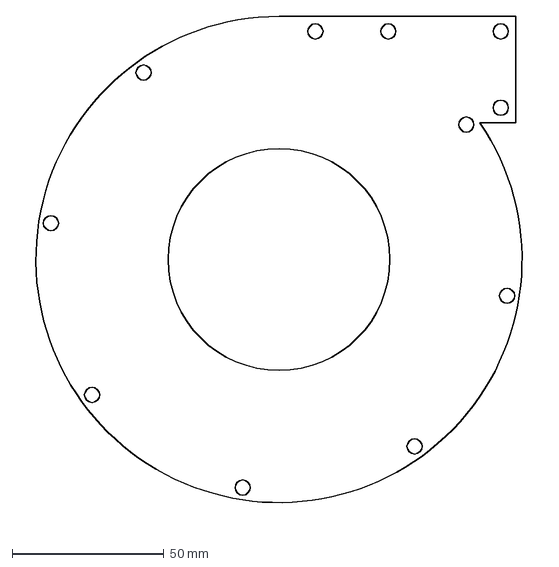
[picture p101: CAD file, 2020-08-04]
Pump/138mm/DXF/pump stator/end plate 1.DXF
173.3 x 167.9 mm
