zenmanenergy/TeslaTurbine/Pump/138mm/Solidworks 2015/magnetic bearings/25x16x5 neodymium bearing.SLDPRT

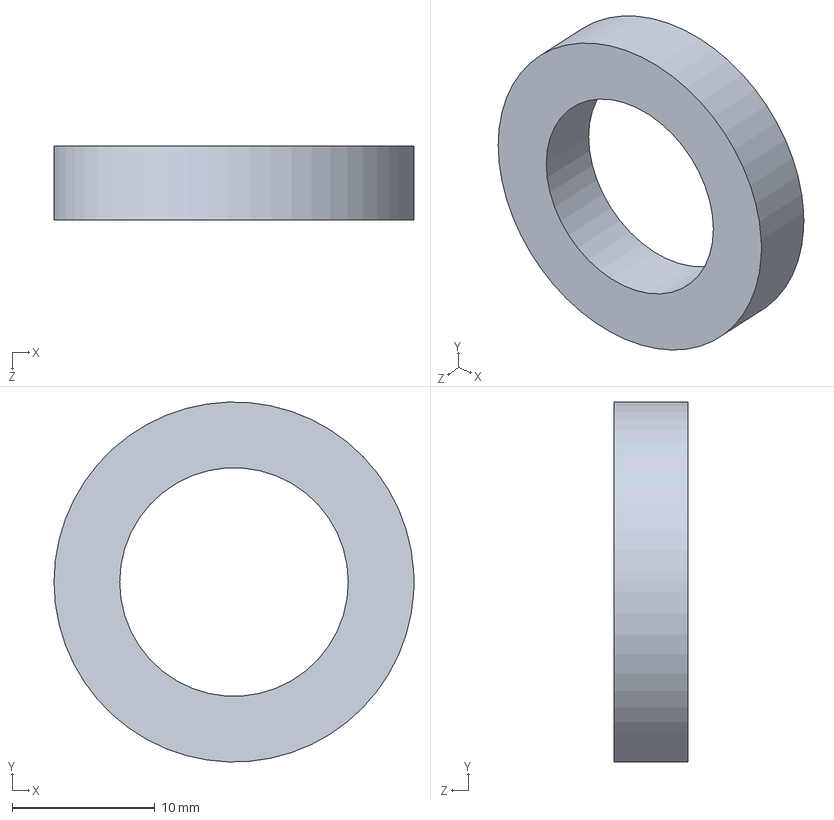
[picture p102: CAD file, 2020-10-07]
Pump/138mm/Solidworks 2015/magnetic bearings/25x16x5 neodymium bearing.SLDPRT
25.2 x 25.2 x 5.20 mm
