zenmanenergy/TeslaTurbine/Pump/138mm/Solidworks 2015/pump stator/bearing pipe.SLDPRT

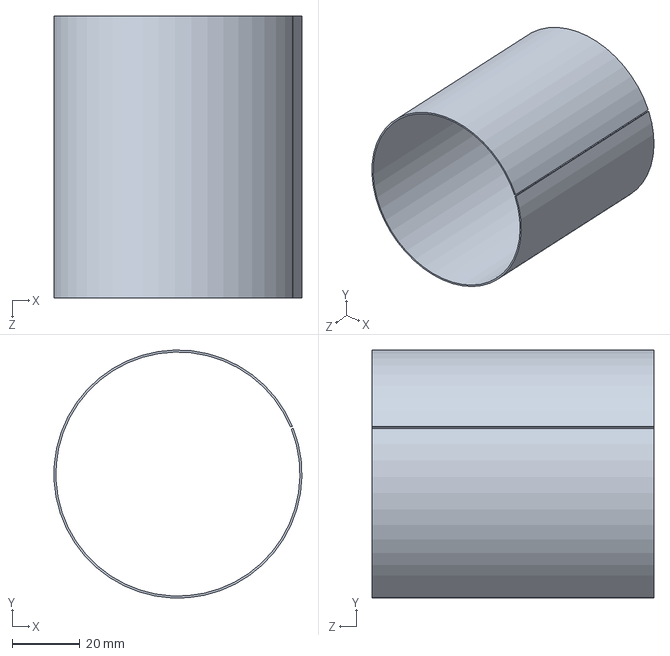
[picture p103: CAD file, 2020-08-22]
Pump/138mm/Solidworks 2015/pump stator/bearing pipe.SLDPRT
73.0 x 73.0 x 83.0 mm
