zenmanenergy/TeslaTurbine/Pump/100mm/DXF/pump stator/input mount 1.DXF

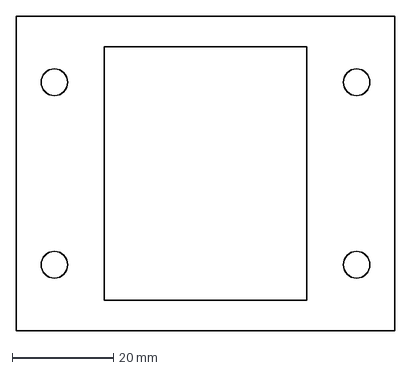
[picture p104: CAD file, 2020-06-16]
Pump/100mm/DXF/pump stator/input mount 1.DXF
74.6 x 62.0 mm
