zenmanenergy/TeslaTurbine/Pump/100mm/Solidworks 2015/pump stator/housing exhaust 2.SLDPRT

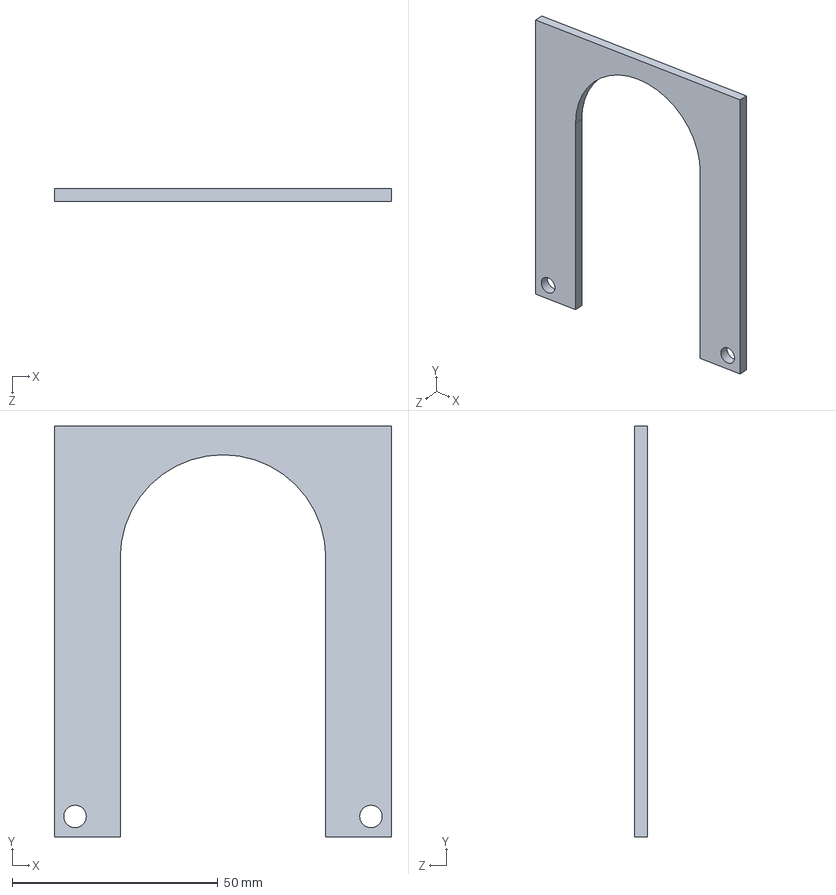
[picture p105: CAD file, 2020-06-29]
Pump/100mm/Solidworks 2015/pump stator/housing exhaust 2.SLDPRT
82.0 x 100.0 x 3.20 mm
