zenmanenergy/TeslaTurbine/Pump/100mm/DXF/pump stator/housing exhaust 2.DXF

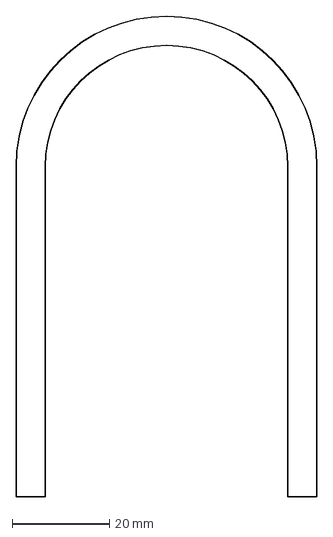
[picture p106: CAD file, 2020-06-16]
Pump/100mm/DXF/pump stator/housing exhaust 2.DXF
62.0 x 99.0 mm
