zenmanenergy/TeslaTurbine/Pump/100mm/Solidworks 2015/pump stator/housing4.SLDPRT

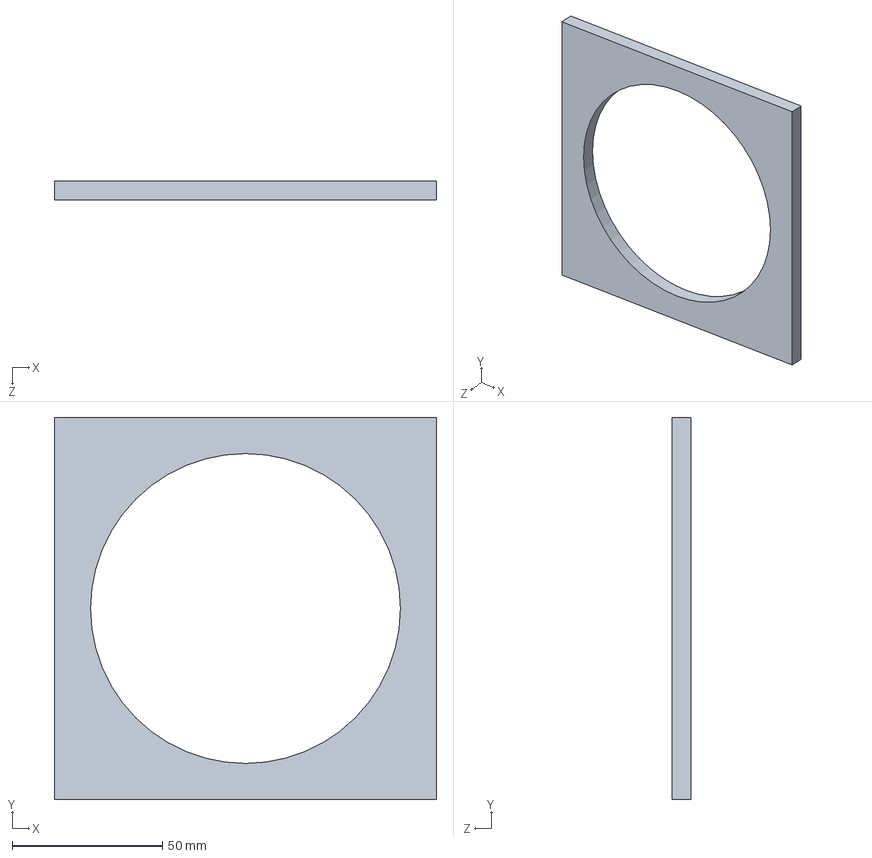
[picture p107: CAD file, 2020-06-16]
Pump/100mm/Solidworks 2015/pump stator/housing4.SLDPRT
127.0 x 127.0 x 6.35 mm
