zenmanenergy/TeslaTurbine/Pump/100mm/DXF/pump stator/housing4.DXF

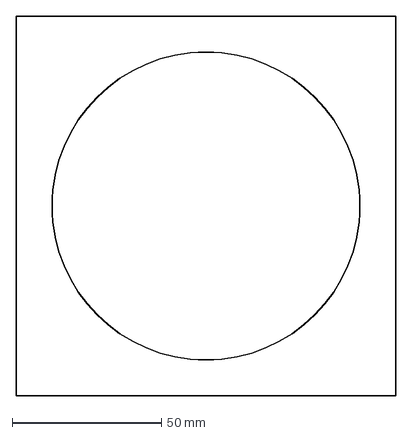
[picture p108: CAD file, 2020-06-16]
Pump/100mm/DXF/pump stator/housing4.DXF
127.0 x 127.0 mm
