zenmanenergy/TeslaTurbine/Pump/100mm/DXF/pump stator/housing1.DXF

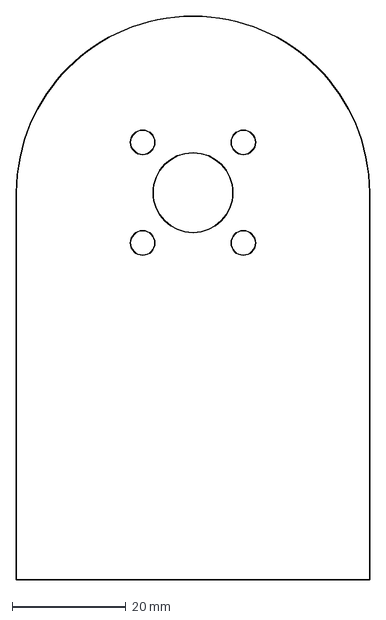
[picture p109: CAD file, 2020-06-16]
Pump/100mm/DXF/pump stator/housing1.DXF
62.0 x 99.0 mm
