zenmanenergy/TeslaTurbine/Pump/100mm/Solidworks 2015/pump stator/exhaust mount.SLDPRT

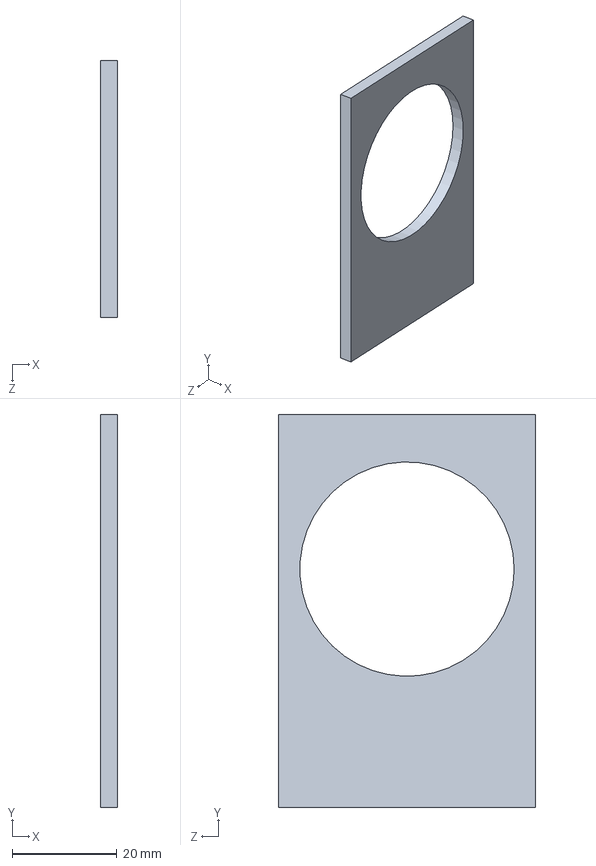
[picture p110: CAD file, 2020-06-16]
Pump/100mm/Solidworks 2015/pump stator/exhaust mount.SLDPRT
3.20 x 75.0 x 49.0 mm
