zenmanenergy/TeslaTurbine/Pump/100mm/Solidworks 2015/pump stator/housing2.SLDPRT

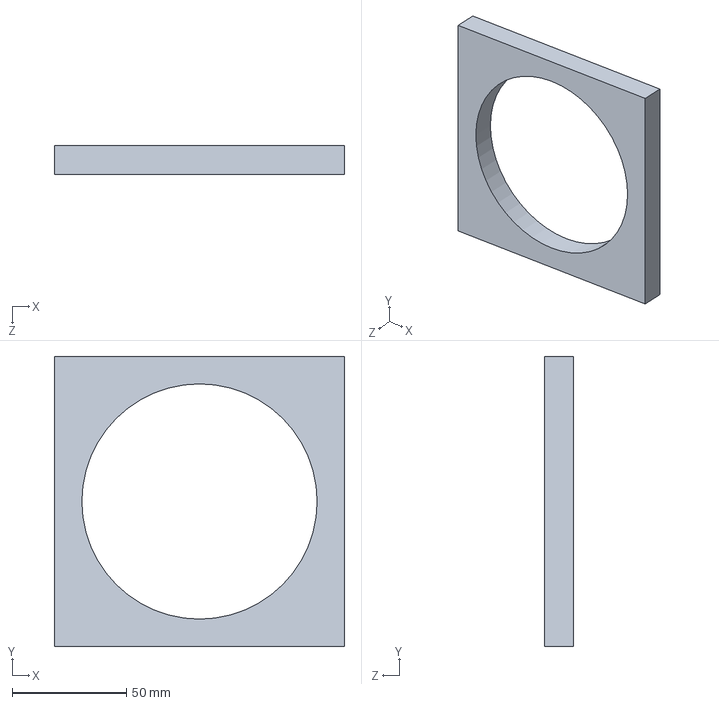
[picture p112: CAD file, 2020-06-16]
Pump/100mm/Solidworks 2015/pump stator/housing2.SLDPRT
127.0 x 127.0 x 12.7 mm
