zenmanenergy/TeslaTurbine/Pump/100mm/Solidworks 2015/pump stator/housing input.SLDPRT

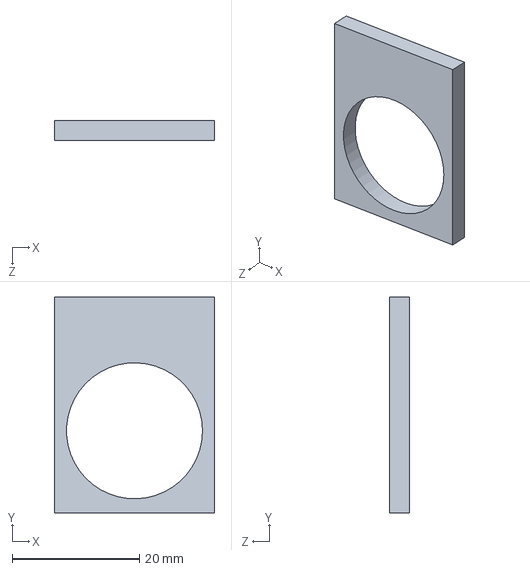
[picture p113: CAD file, 2020-06-16]
Pump/100mm/Solidworks 2015/pump stator/housing input.SLDPRT
25.2 x 34.0 x 3.20 mm
